BRG-research/compas_tf/data/FloorColumnConnection/4x/Artboard 1@4x.png

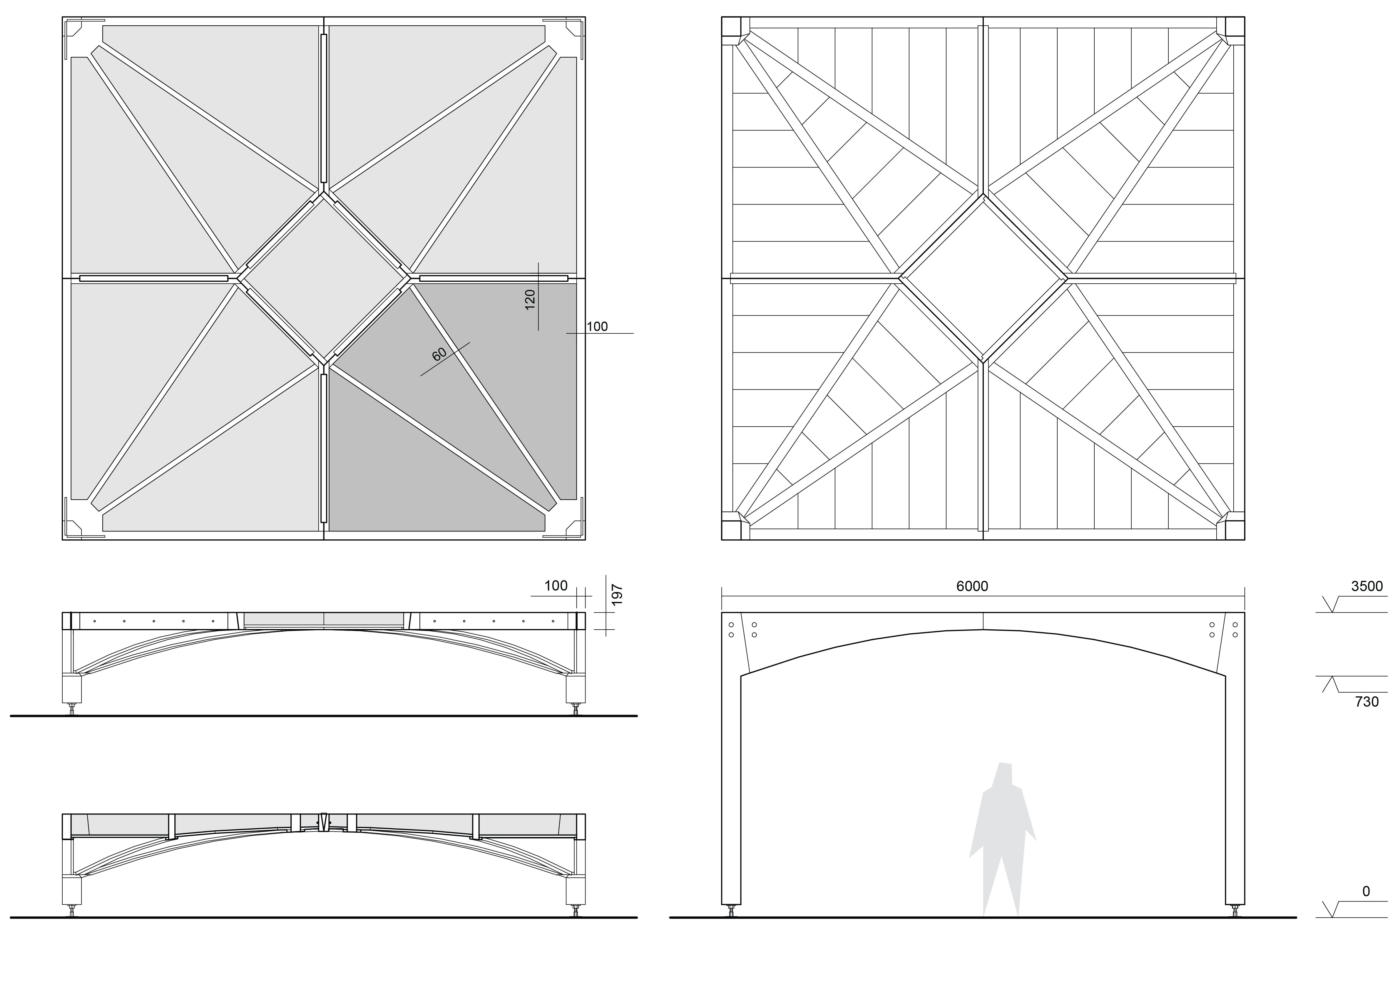
data/FloorColumnConnection/4x/Artboard 1@4x.png
