BRG-research/compas_tf/data/FloorColumnConnection/drawings.png

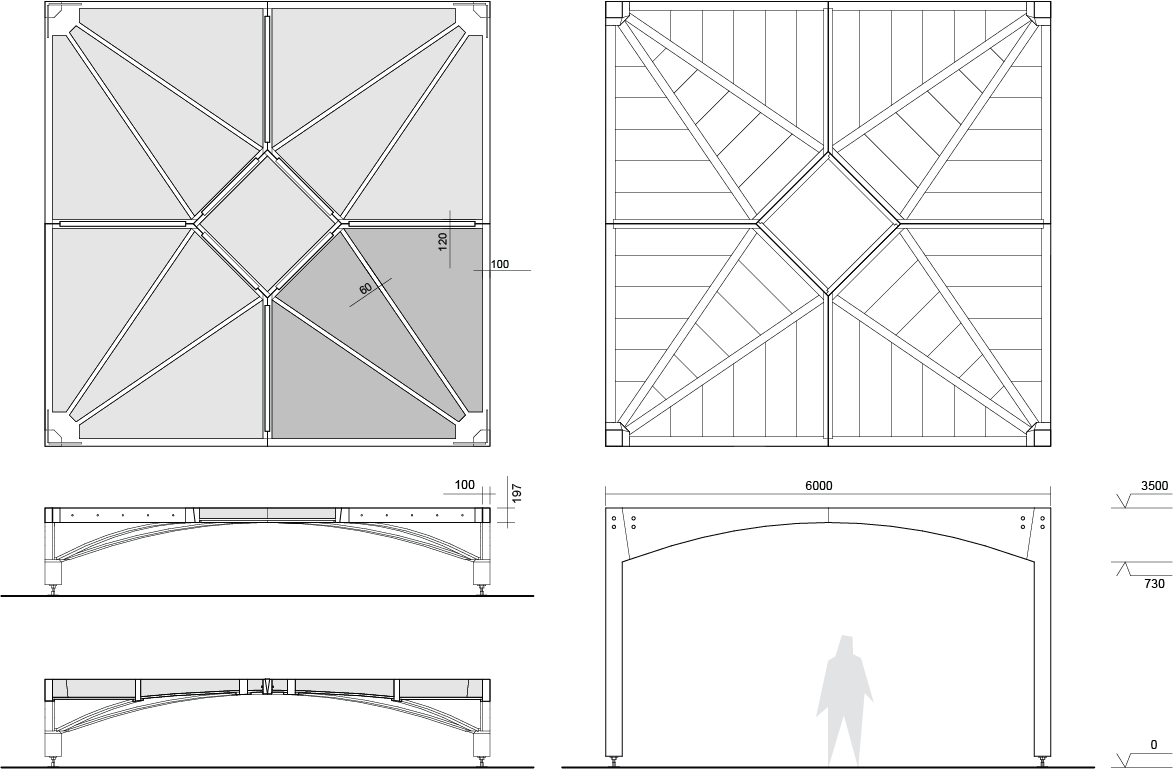
data/FloorColumnConnection/drawings.png
