BRG-research/compas_tf/data/total_station/total_station_es105_preview.jpg

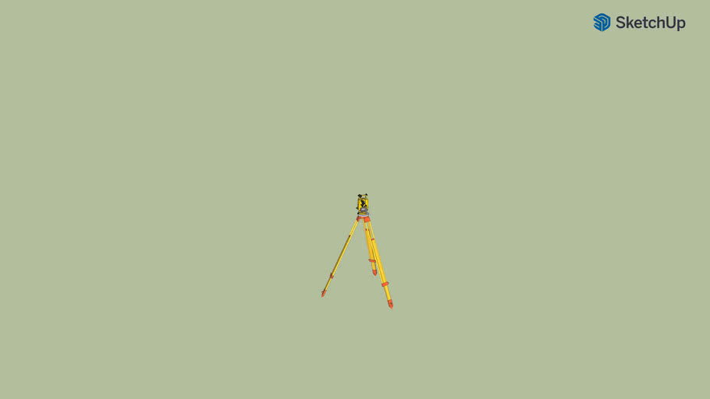
data/total_station/total_station_es105_preview.jpg
