BRG-research/compas_tf/docs/_images/1767874582386.jpg

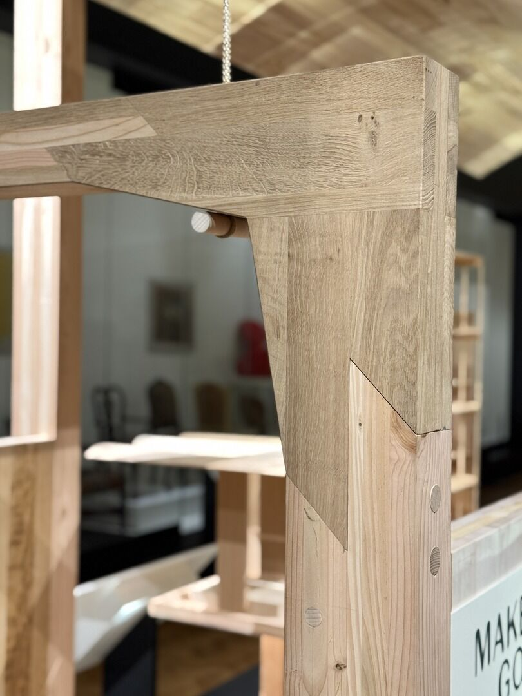
docs/_images/1767874582386.jpg
