BRG-research/compas_tf/docs/_images/column_head_connection3.png

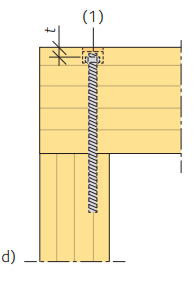
docs/_images/column_head_connection3.png
