BRG-research/compas_tf/docs/_images/column_head_connection.png

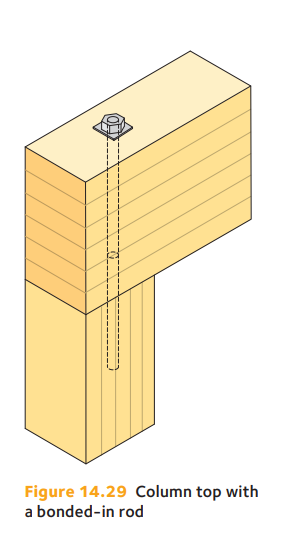
docs/_images/column_head_connection.png
