BRG-research/compas_tf/docs/_images/compresseion_perpendicular_to_grain.jpg

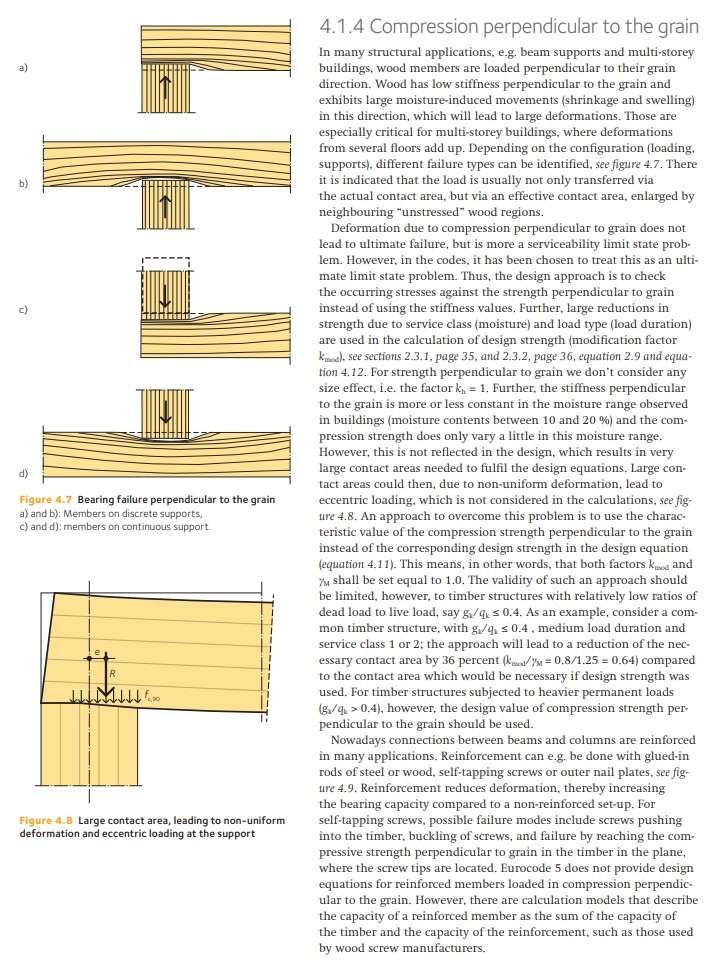
docs/_images/compresseion_perpendicular_to_grain.jpg
