BRG-research/compas_tf/docs/_images/compresseion_perpendicular_to_grain_2.jpg

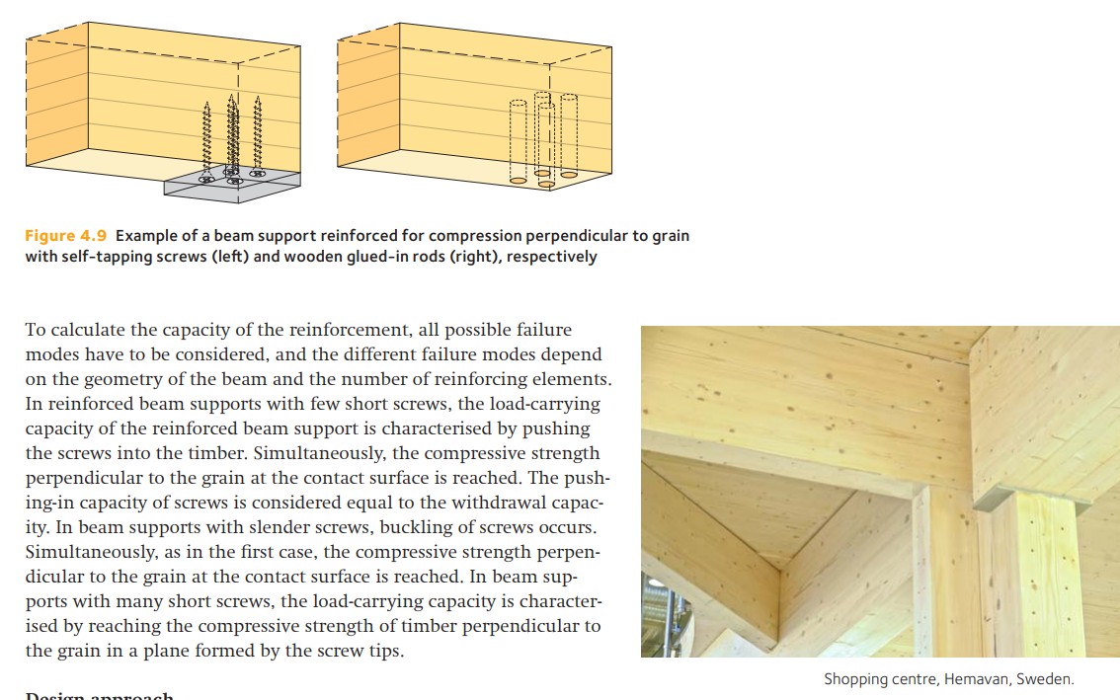
docs/_images/compresseion_perpendicular_to_grain_2.jpg
