BRG-research/compas_tf/docs/_images/icd_column_head_clt_fiber.png

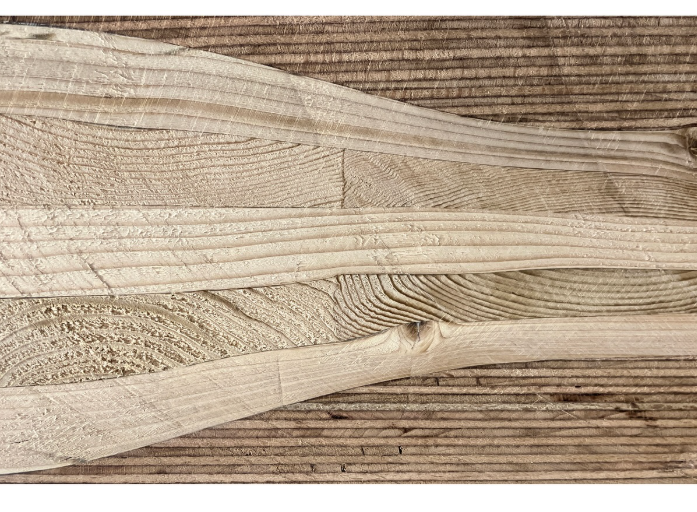
docs/_images/icd_column_head_clt_fiber.png
