BRG-research/compas_tf/docs/_images/model1.png

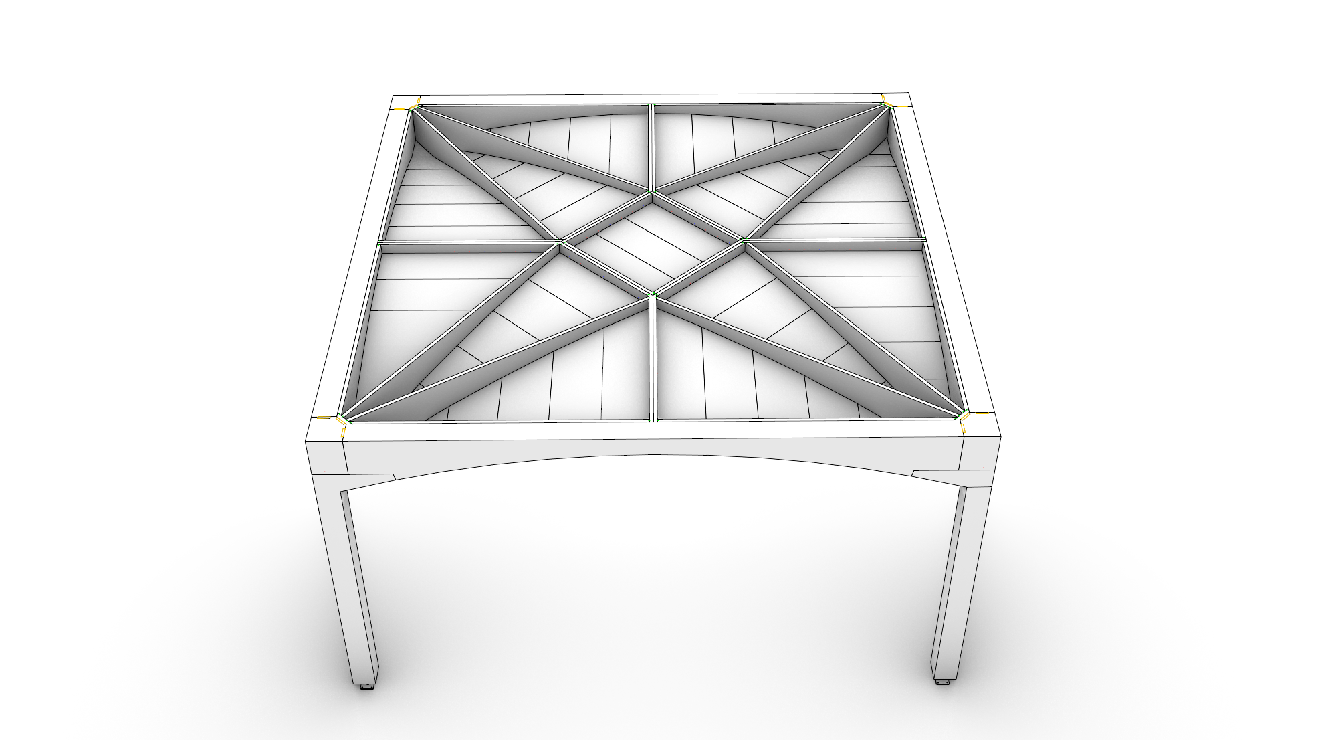
docs/_images/model1.png
