BRG-research/compas_tf/docs/_images/quarter1.png

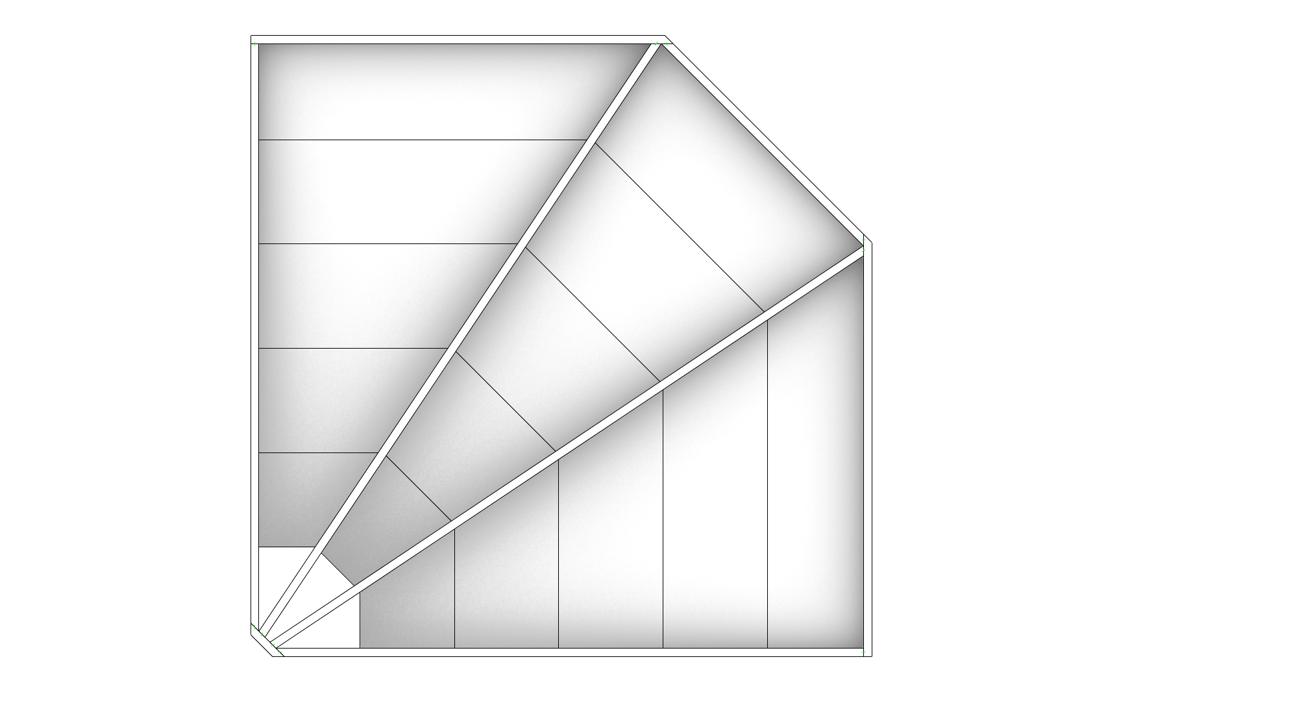
docs/_images/quarter1.png
