BRG-research/compas_tf/docs/_images/quarter2.png

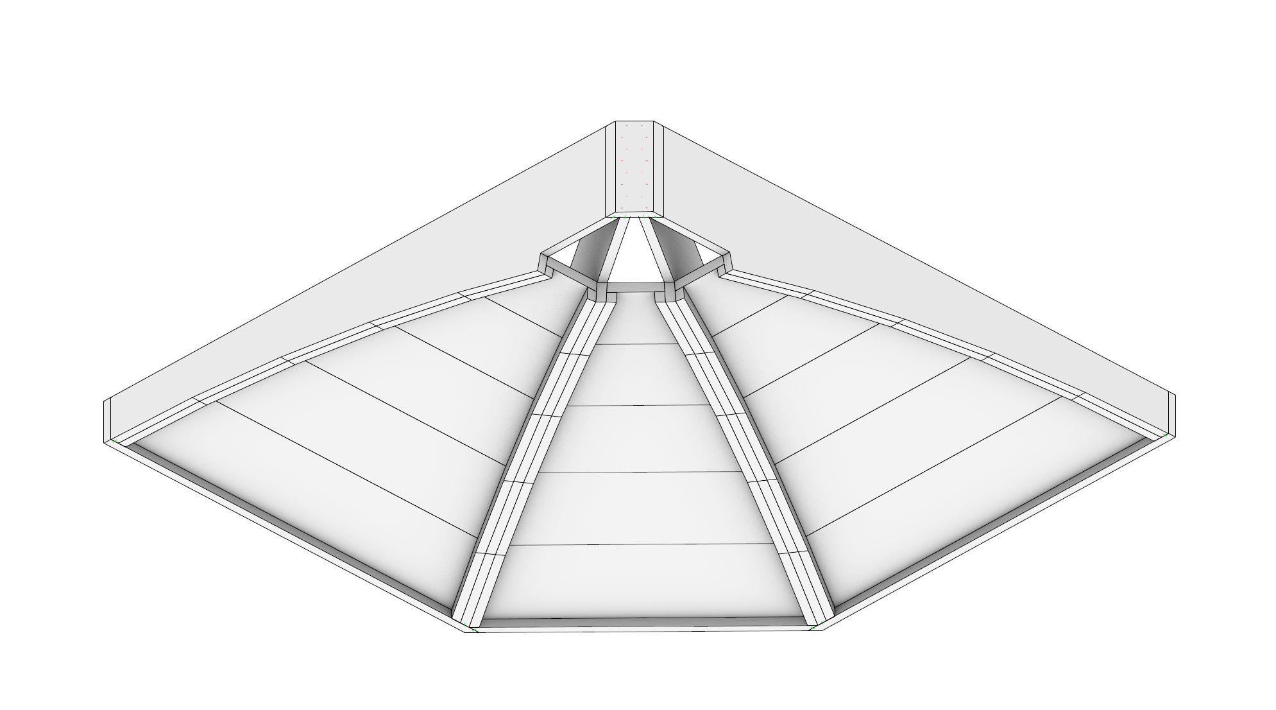
docs/_images/quarter2.png
