BRG-research/compas_tf/docs/_images/quarter3.png

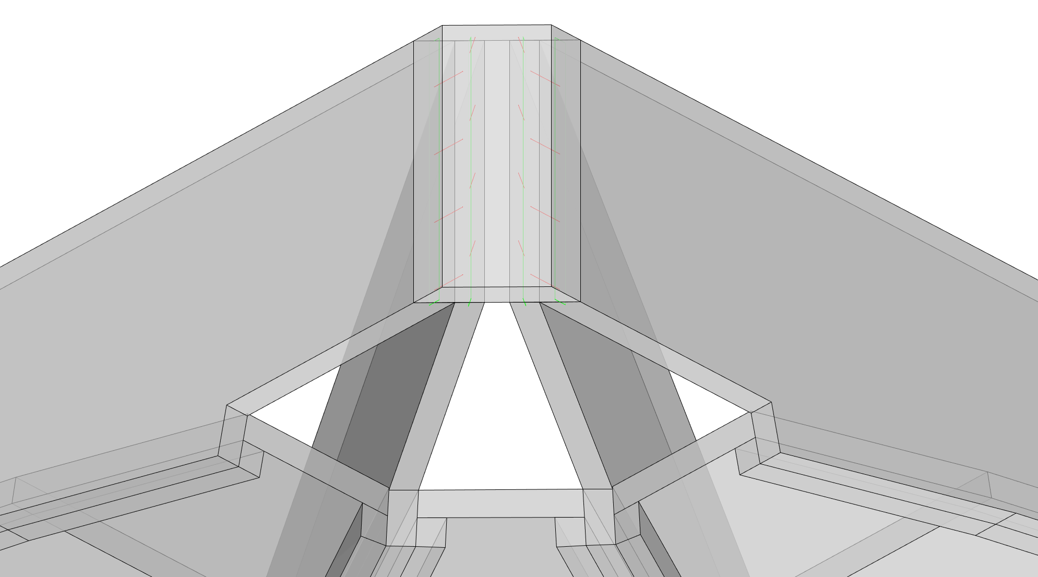
docs/_images/quarter3.png
