BRG-research/compas_tf/docs/_images/quarter4.png

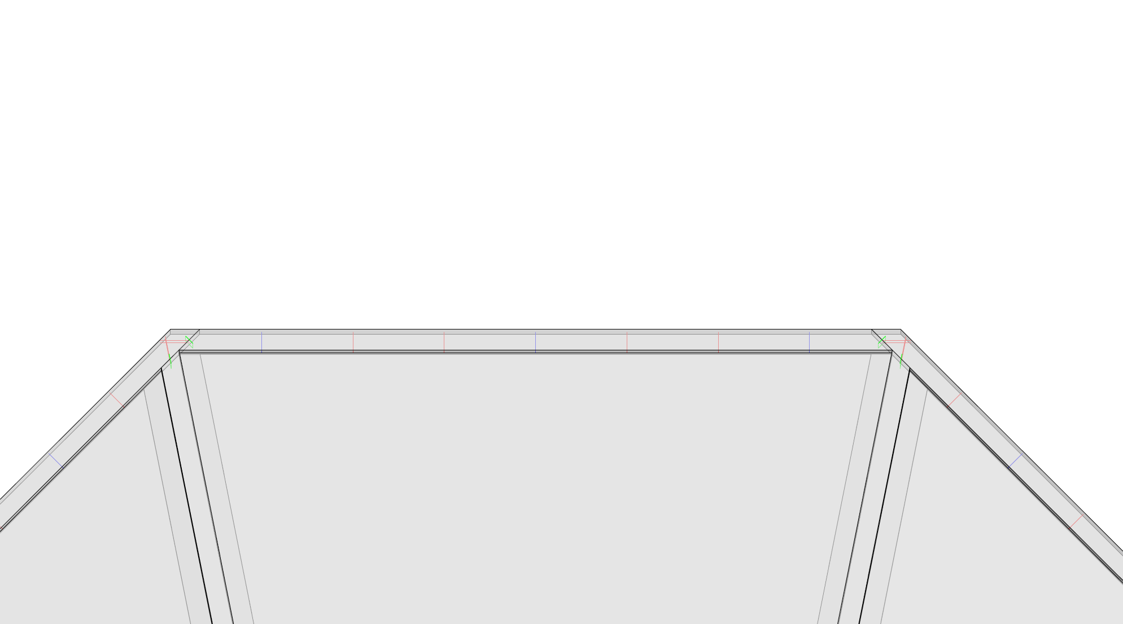
docs/_images/quarter4.png
