BRG-research/compas_tf/docs/_images/robeller_reciprocal.jpg

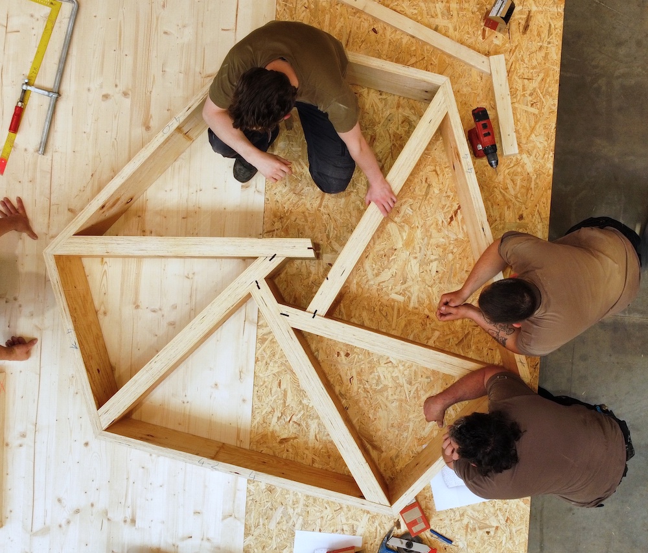
docs/_images/robeller_reciprocal.jpg
