BRG-research/compas_tf/docs/_images/screenshot_0.png

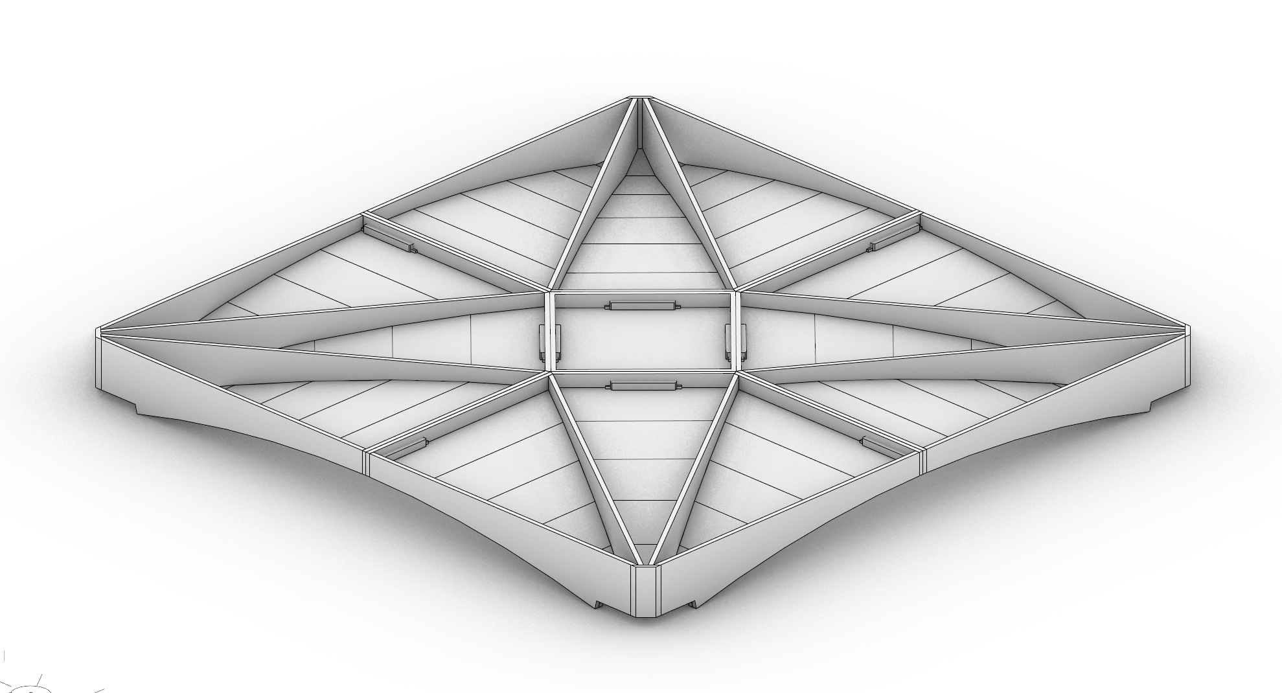
docs/_images/screenshot_0.png
