BRG-research/compas_tf/docs/_images/screenshot_1.png

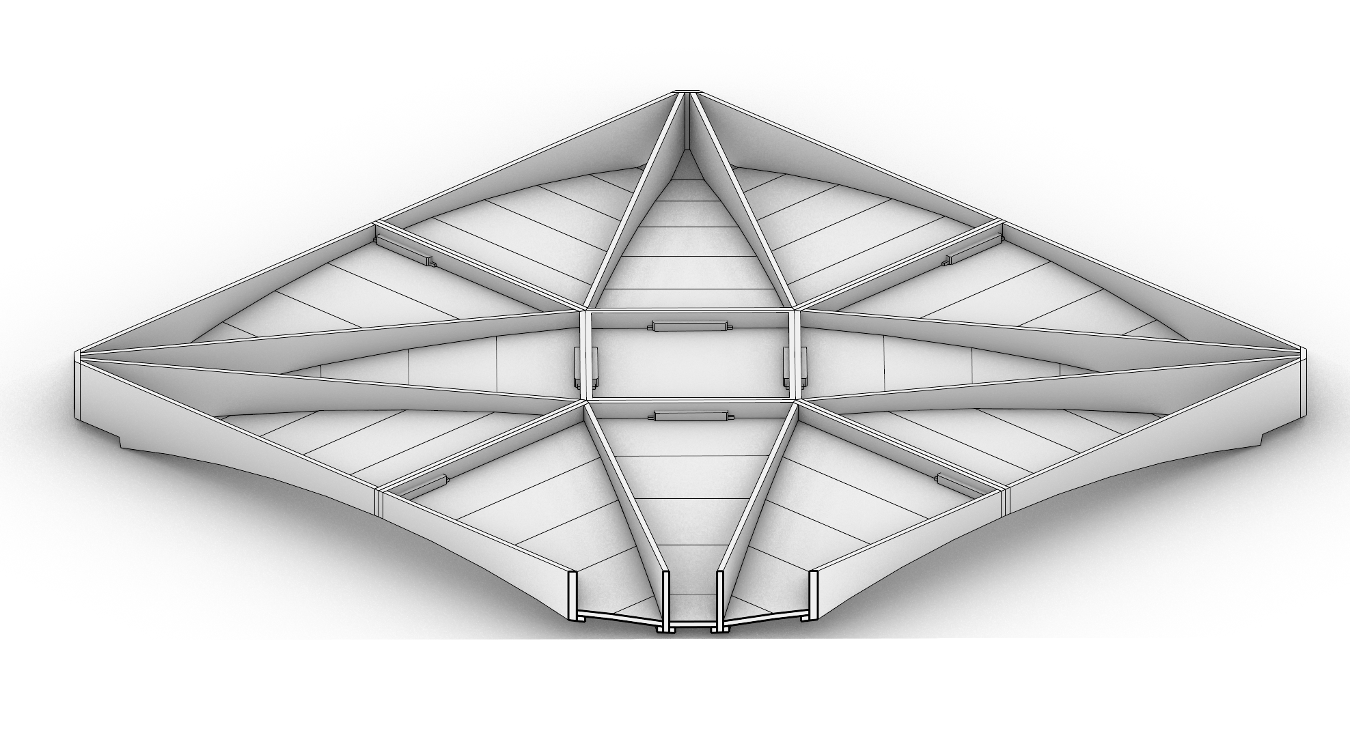
docs/_images/screenshot_1.png
