BRG-research/compas_tf/docs/_images/screenshot_2.png

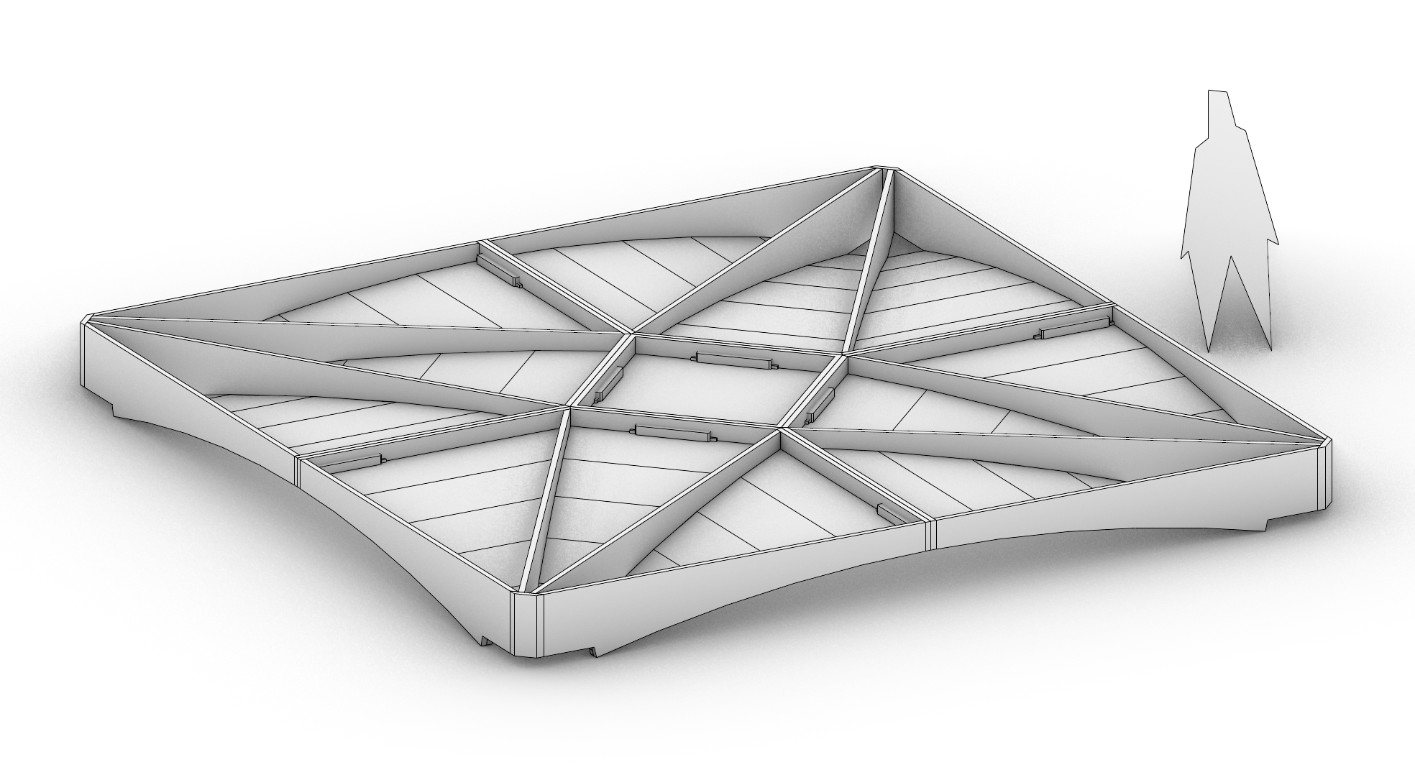
docs/_images/screenshot_2.png
