BRG-research/compas_tf/docs/_images/screenshot_3.png

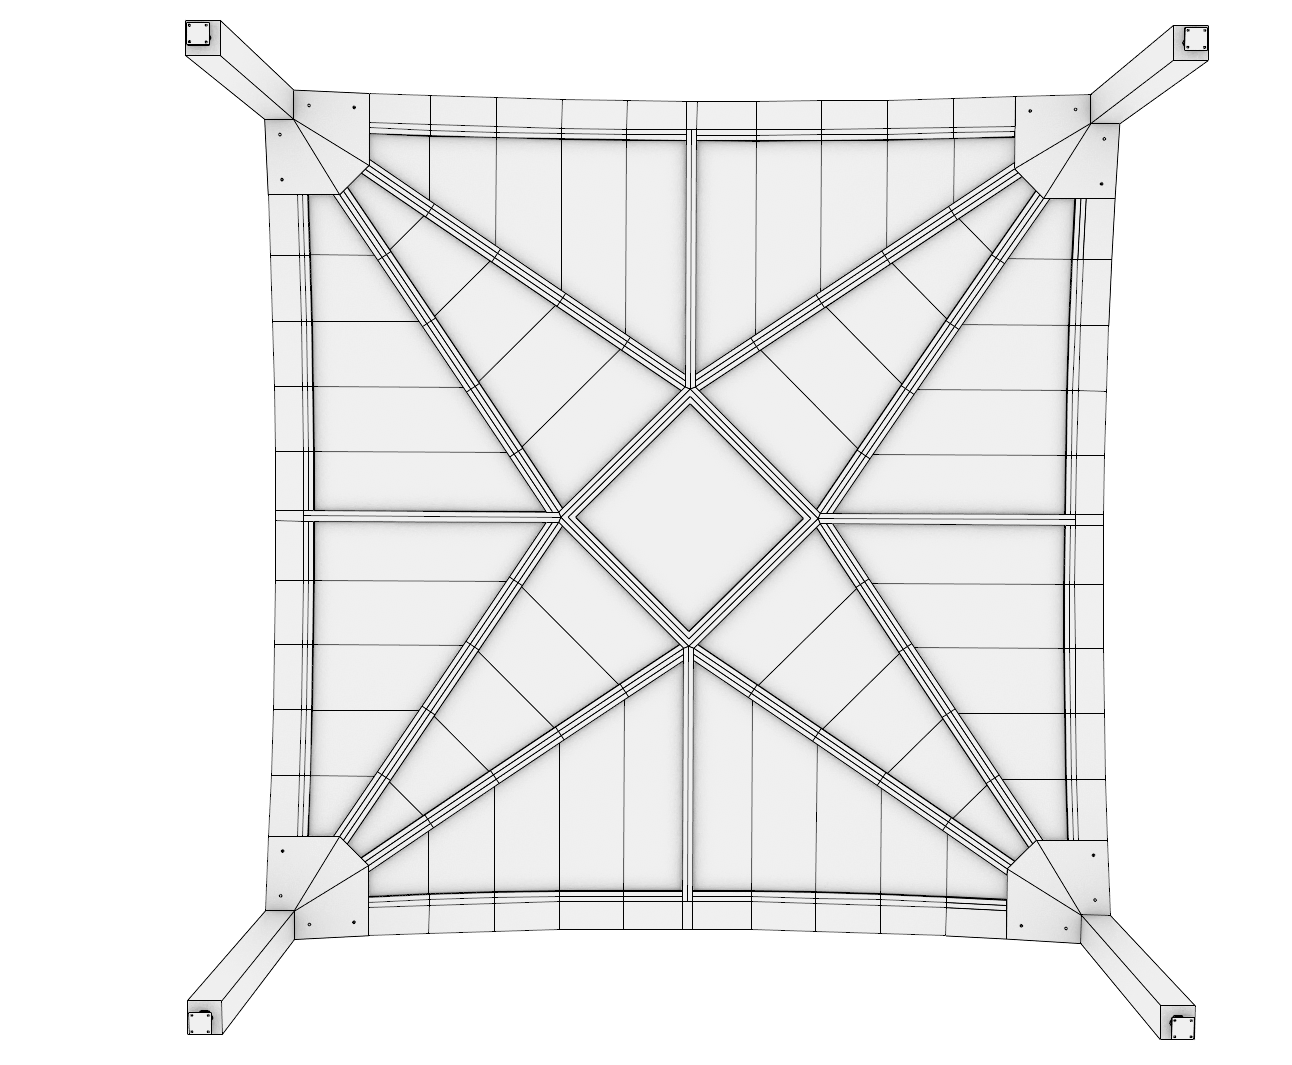
docs/_images/screenshot_3.png
