BRG-research/compas_tf/docs/_images/screenshot_5.png

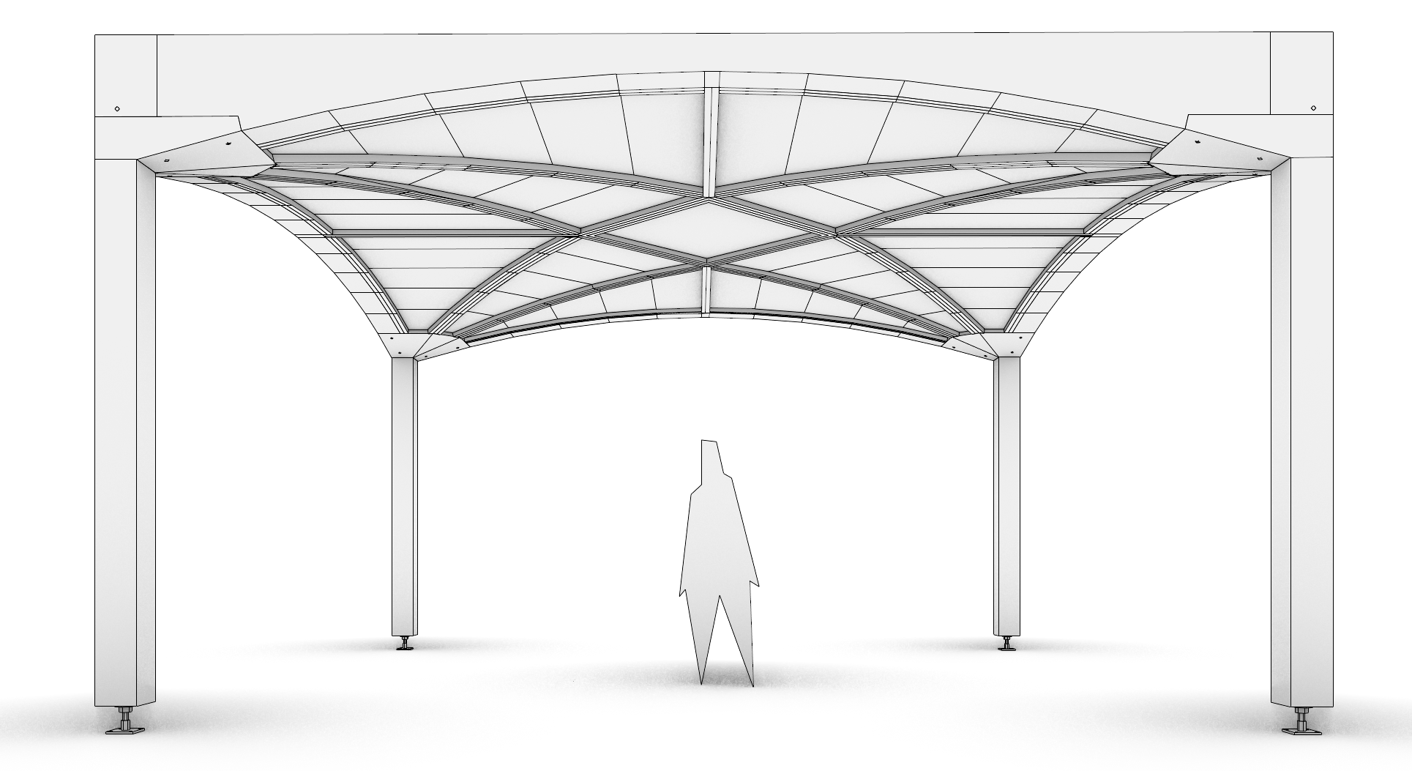
docs/_images/screenshot_5.png
