BRG-research/compas_tf/docs/references/autobahn_a1_pirmin_jung.png

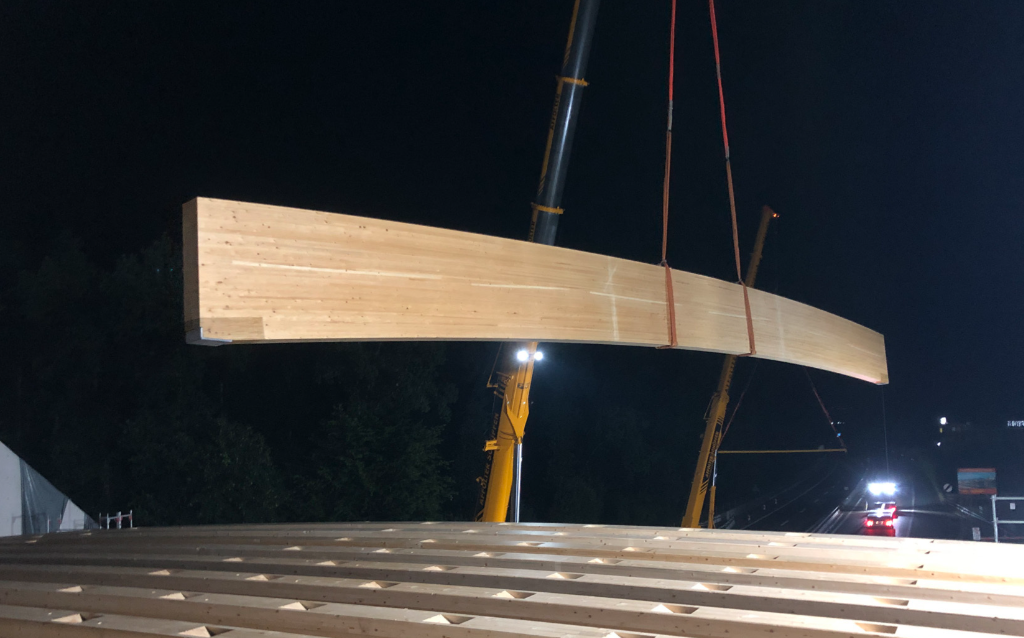
docs/references/autobahn_a1_pirmin_jung.png
