BRG-research/compas_tf/src/compas_tf/data/column_base_power_base_sherpa_150402_PB_L-140-C.obj

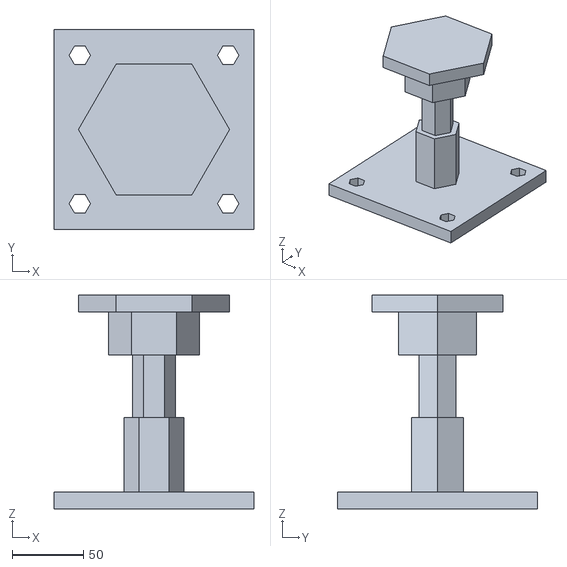
[picture p47: CAD file, 2026-01-28]
src/compas_tf/data/column_base_power_base_sherpa_150402_PB_L-140-C.obj
140.0 x 140.0 x 150.0
