BRG-research/compas_tf/src/compas_tf/data/OuterRibConnector/OuterRibConnector_Result.obj

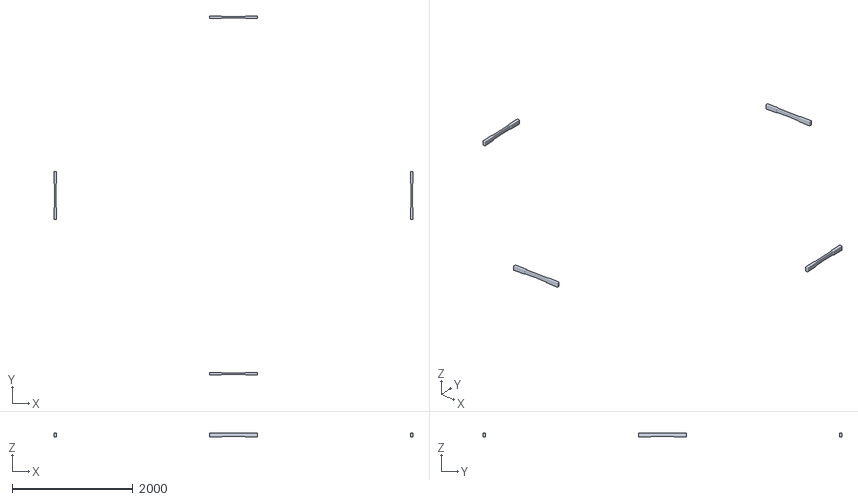
[picture p48: CAD file, 2026-08-09]
src/compas_tf/data/OuterRibConnector/OuterRibConnector_Result.obj
5940.0 x 5940.0 x 70.4
