BRG-research/compas_tf/data/column_base_power_base_sherpa_150402_PB_L-140-C.ply

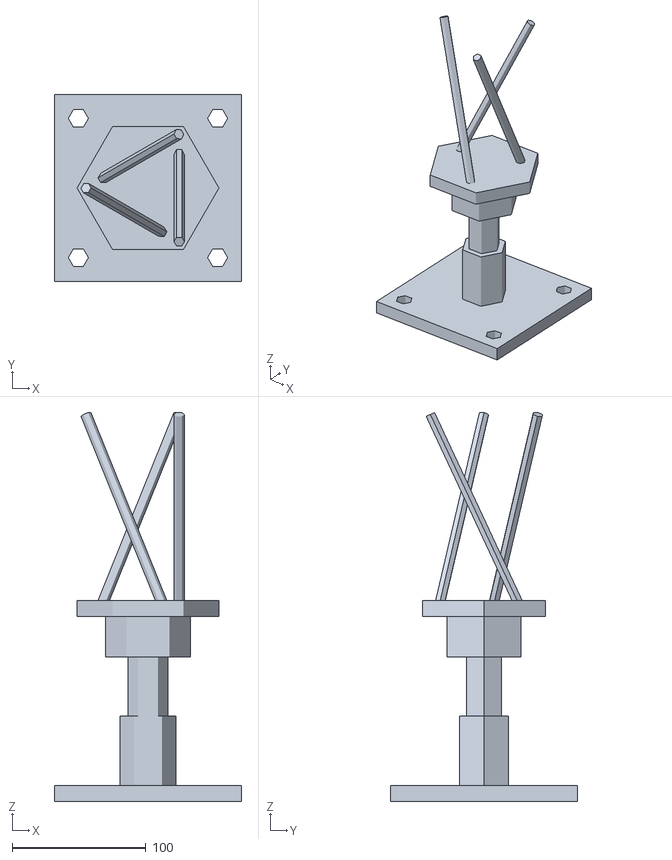
[picture p49: CAD file, 2026-01-28]
data/column_base_power_base_sherpa_150402_PB_L-140-C.ply
140.0 x 140.0 x 290.6
