BRG-research/compas_tf/data/fabrication/wedges_inner_beams_0_fab.stp

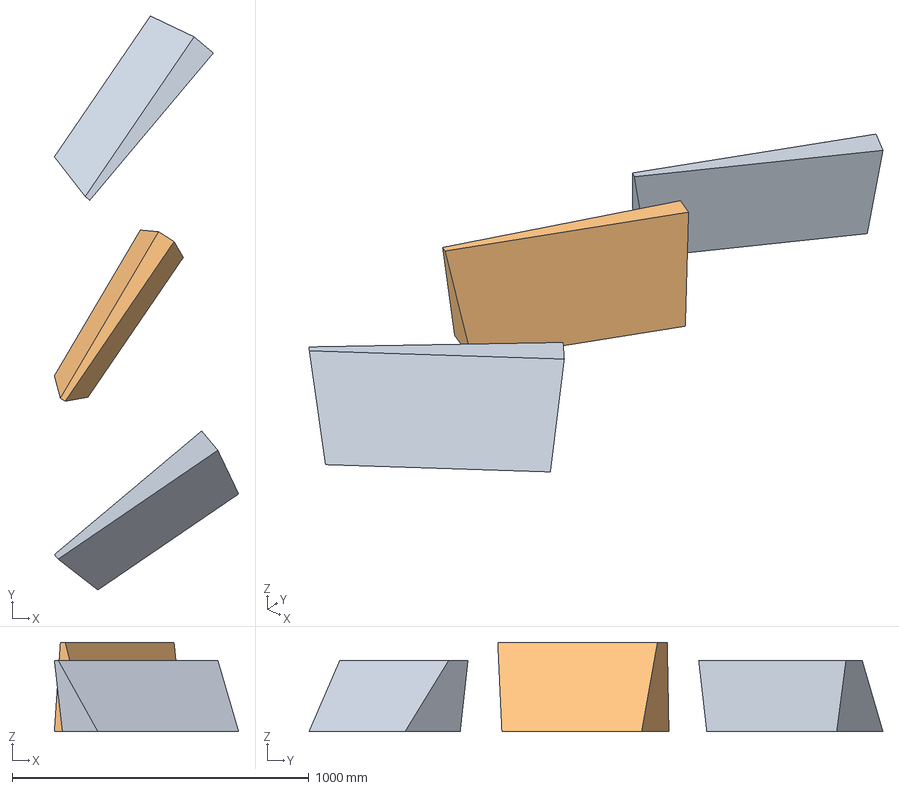
[picture p50: CAD file, 2026-08-25]
data/fabrication/wedges_inner_beams_0_fab.stp
620.7 x 1932.8 x 300.0 mm
wedges_inner_beams_0_fab 1.1
wedges_inner_beams_0_fab 1.2
wedges_inner_beams_0_fab 1.3
wedges_inner_beams_0_fab 1.4
wedges_inner_beams_0_fab 1.5
wedges_inner_beams_0_fab 1.6
