BRG-research/compas_tf/data/SchoringElement/schoring_vertical_body_start_0.obj

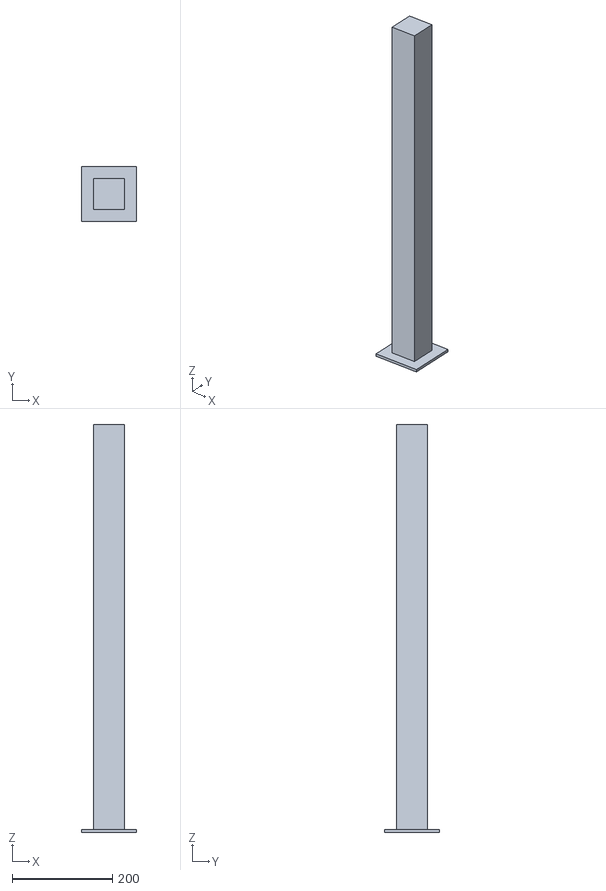
[picture p51: CAD file, 2026-04-22]
data/SchoringElement/schoring_vertical_body_start_0.obj
110.0 x 110.0 x 814.0
