BRG-research/compas_tf/src/compas_tf/data/OuterRibConnector/OuterRibConnector.obj

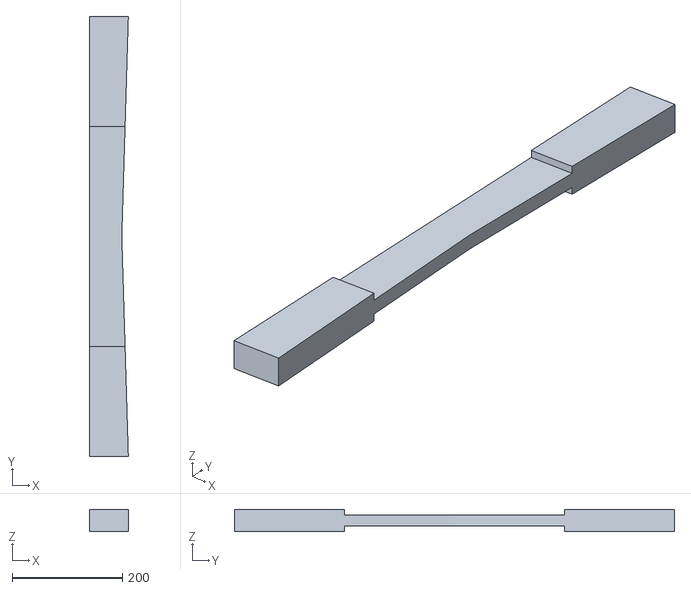
[picture p52: CAD file, 2026-08-09]
src/compas_tf/data/OuterRibConnector/OuterRibConnector.obj
70.4 x 800.0 x 40.0
