BRG-research/compas_tf/data/fabrication/column_0_preview.obj

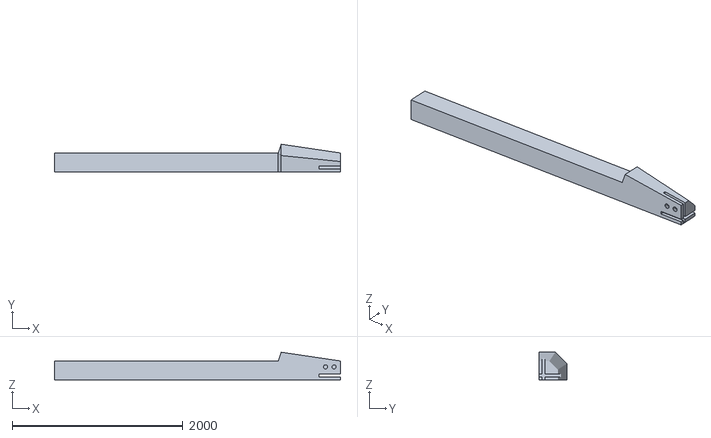
[picture p54: CAD file, 2026-08-25]
data/fabrication/column_0_preview.obj
3350.0 x 323.0 x 323.0
