BRG-research/compas_tf/src/compas_tf/data/OuterRibConnector/OuterRibConnector_cut0.obj

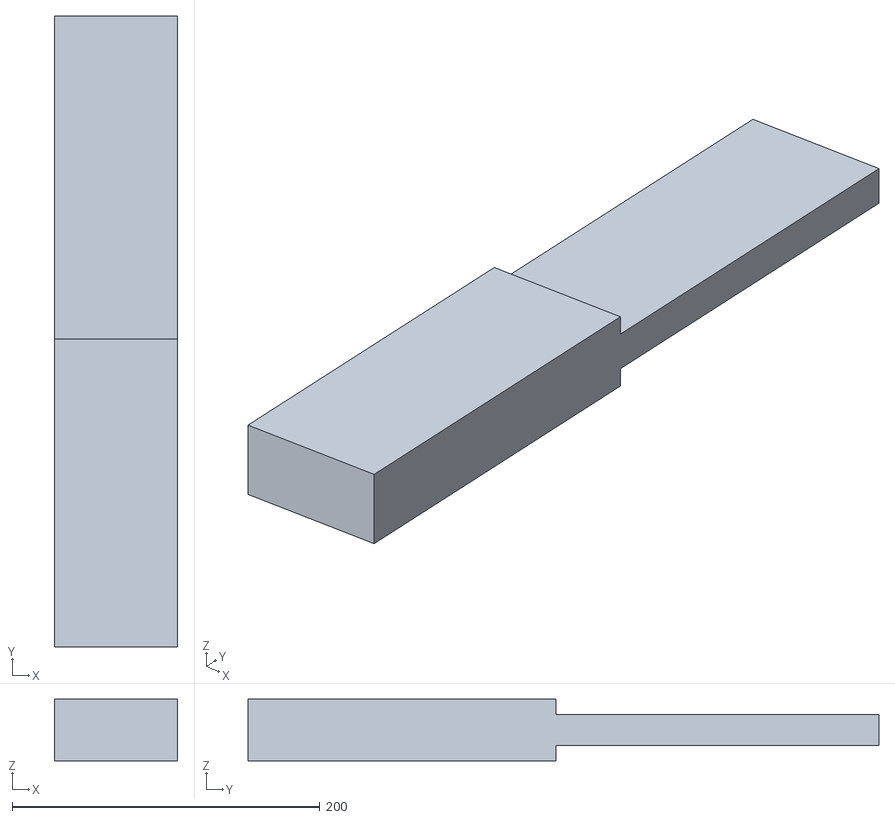
[picture p56: CAD file, 2026-08-09]
src/compas_tf/data/OuterRibConnector/OuterRibConnector_cut0.obj
80.0 x 410.0 x 40.0
