BRG-research/compas_tf/data/beam_column_head_connection_180413_Sherpa_XL120_8x160_3D_detailed.obj

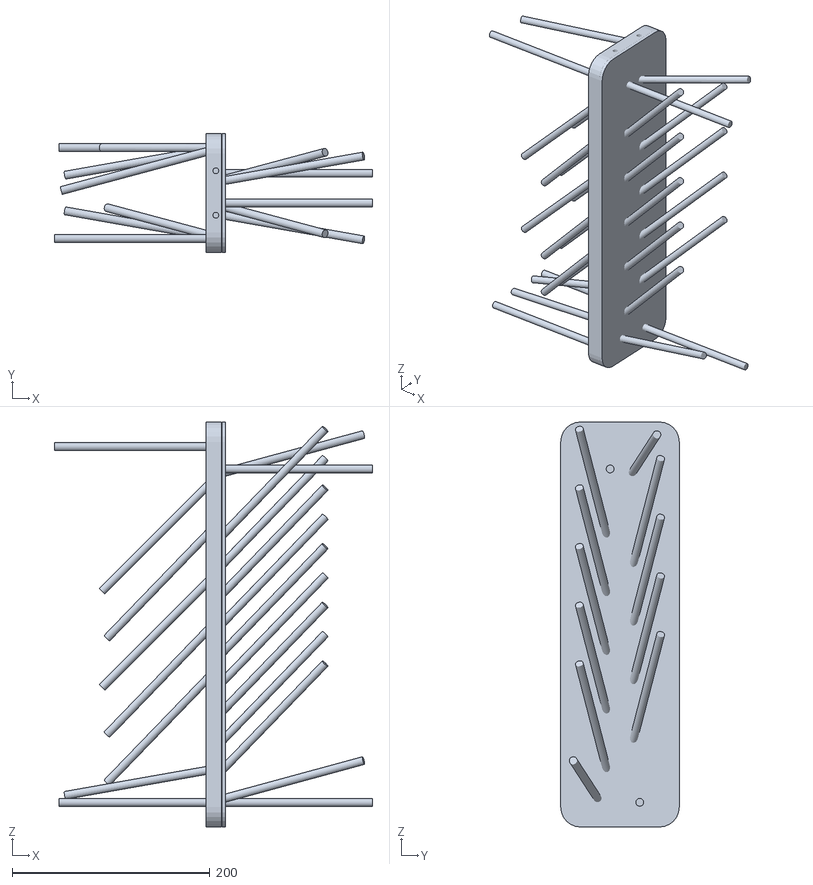
[picture p57: CAD file, 2026-01-28]
data/beam_column_head_connection_180413_Sherpa_XL120_8x160_3D_detailed.obj
322.2 x 120.0 x 410.0
