BRG-research/compas_tf/data/fabrication/connector_0_fab.stp

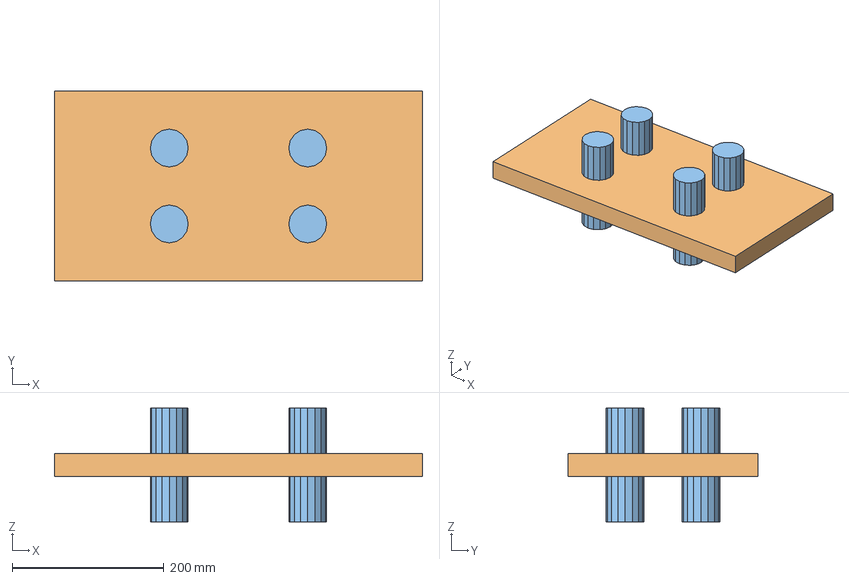
[picture p58: CAD file, 2026-08-25]
data/fabrication/connector_0_fab.stp
485.0 x 250.0 x 150.0 mm
connector_0_fab 1.1
connector_0_fab 1.2
connector_0_fab 1.3
connector_0_fab 1.4
connector_0_fab 1.5
connector_0_fab 1.6
