BRG-research/compas_tf/data/SchoringElement/schoring_vertical_body_end_5.obj

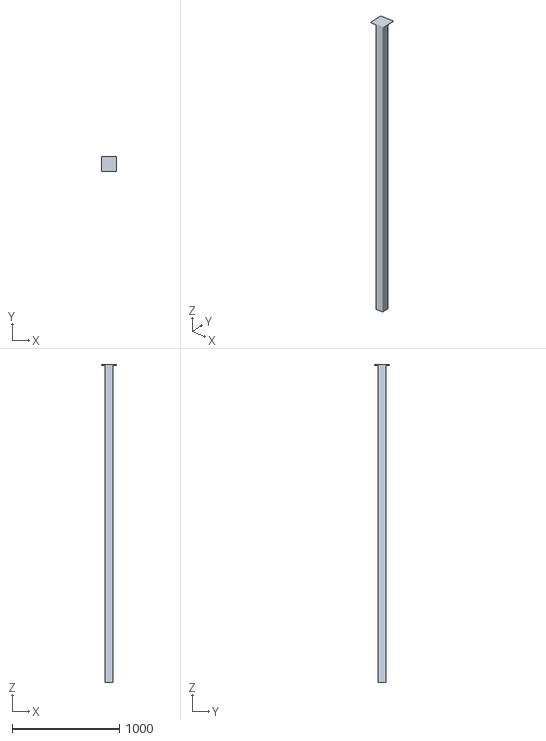
[picture p59: CAD file, 2026-04-22]
data/SchoringElement/schoring_vertical_body_end_5.obj
140.0 x 140.0 x 2965.0
