BRG-research/compas_tf/data/fabrication/connector_0_preview.obj

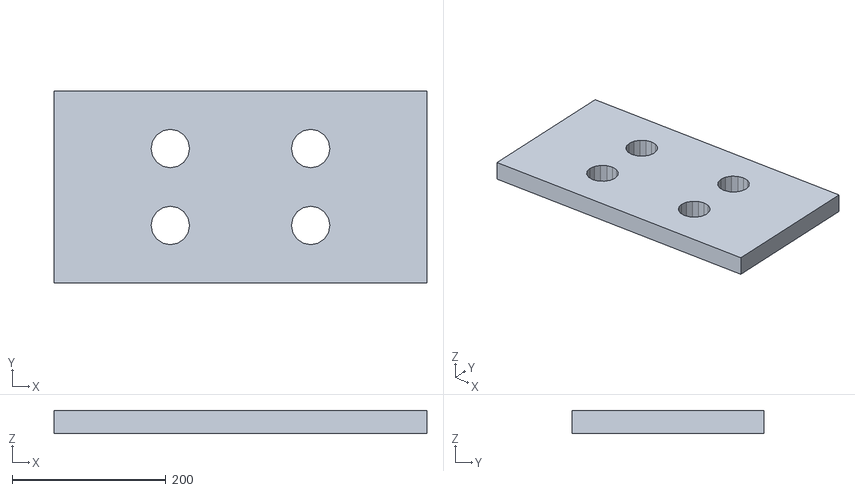
[picture p60: CAD file, 2026-08-25]
data/fabrication/connector_0_preview.obj
485.0 x 250.0 x 30.0
