BRG-research/compas_tf/data/fabrication/inner_beams_2_0_preview.obj

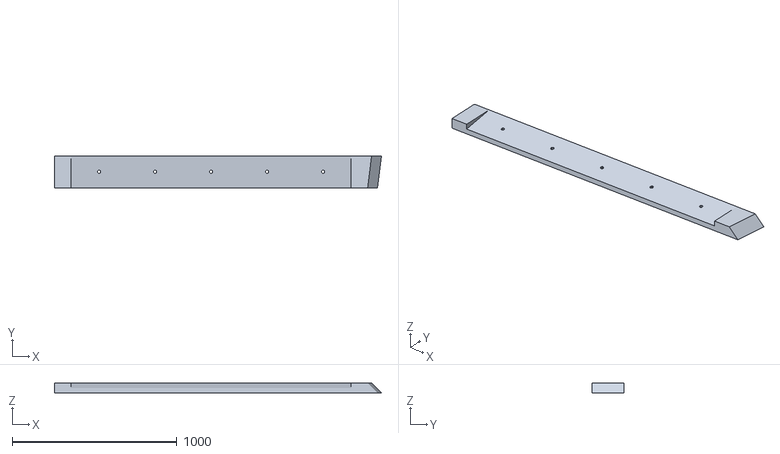
[picture p62: CAD file, 2026-08-25]
data/fabrication/inner_beams_2_0_preview.obj
1984.4 x 197.0 x 60.0
