BRG-research/compas_tf/data/SchoringElement/custom_head0.obj

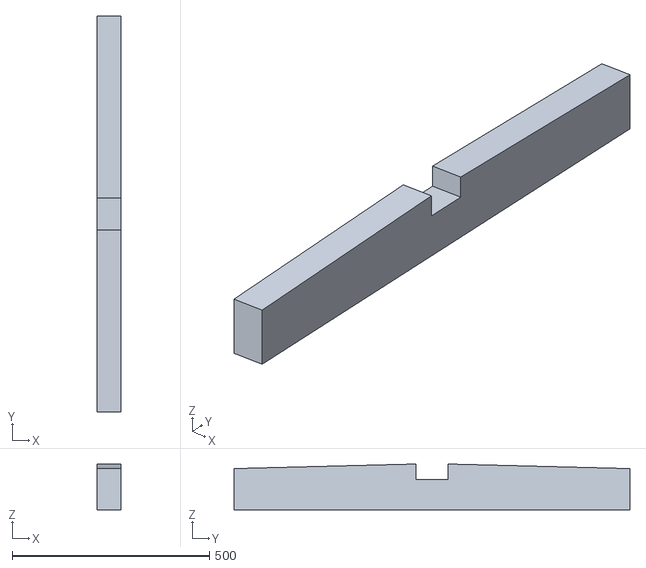
[picture p63: CAD file, 2026-04-22]
data/SchoringElement/custom_head0.obj
60.0 x 1004.0 x 116.6
