BRG-research/compas_tf/data/fabrication/tsections_0_fab.stp

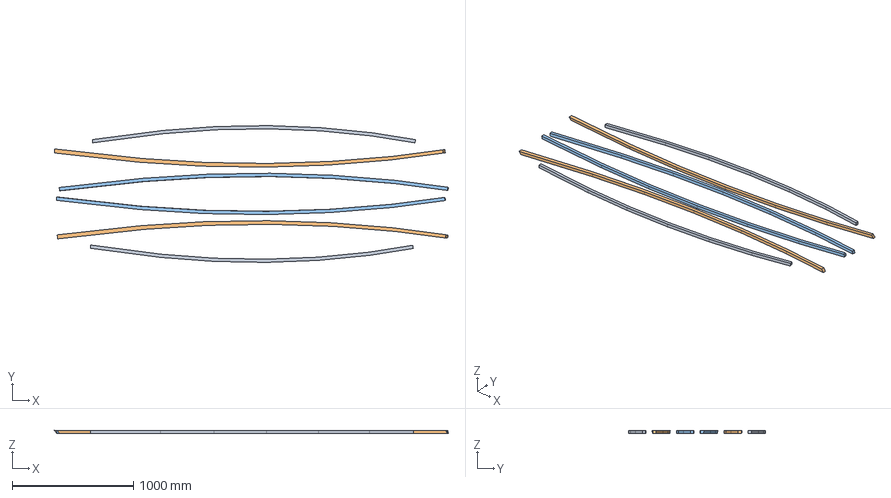
[picture p64: CAD file, 2026-08-25]
data/fabrication/tsections_0_fab.stp
3255.2 x 1130.6 x 27.0 mm
tsections_0_fab 1.1
tsections_0_fab 1.2
tsections_0_fab 1.3
tsections_0_fab 1.4
tsections_0_fab 1.5
tsections_0_fab 1.6
tsections_0_fab 1.7
tsections_0_fab 1.8
tsections_0_fab 1.9
tsections_0_fab 1.10
tsections_0_fab 1.11
tsections_0_fab 1.12
