BRG-research/compas_tf/data/SchoringElement/schoring_vertical_body_end_2.obj

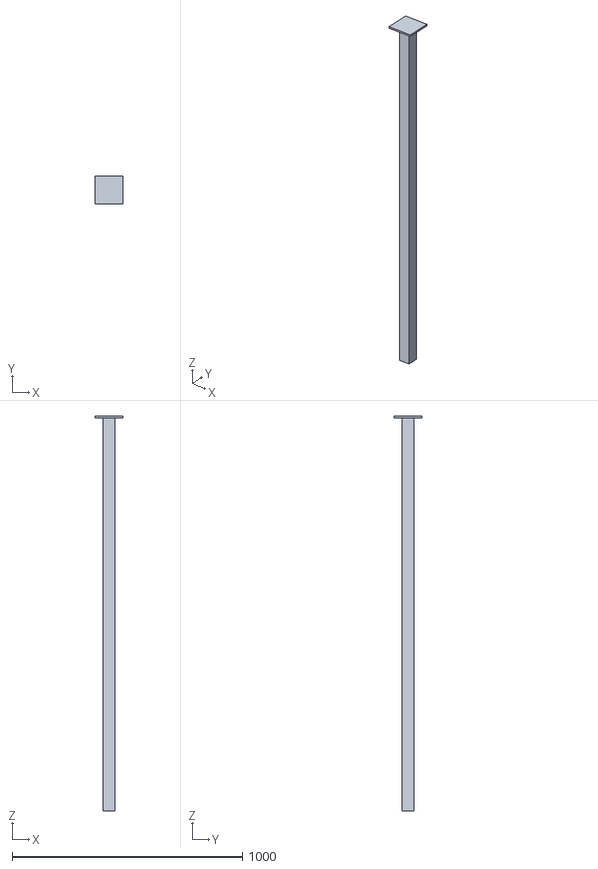
[picture p65: CAD file, 2026-04-22]
data/SchoringElement/schoring_vertical_body_end_2.obj
120.0 x 120.0 x 1715.0
