BRG-research/compas_tf/data/fabrication/inner_beams_0_0_fab.stp

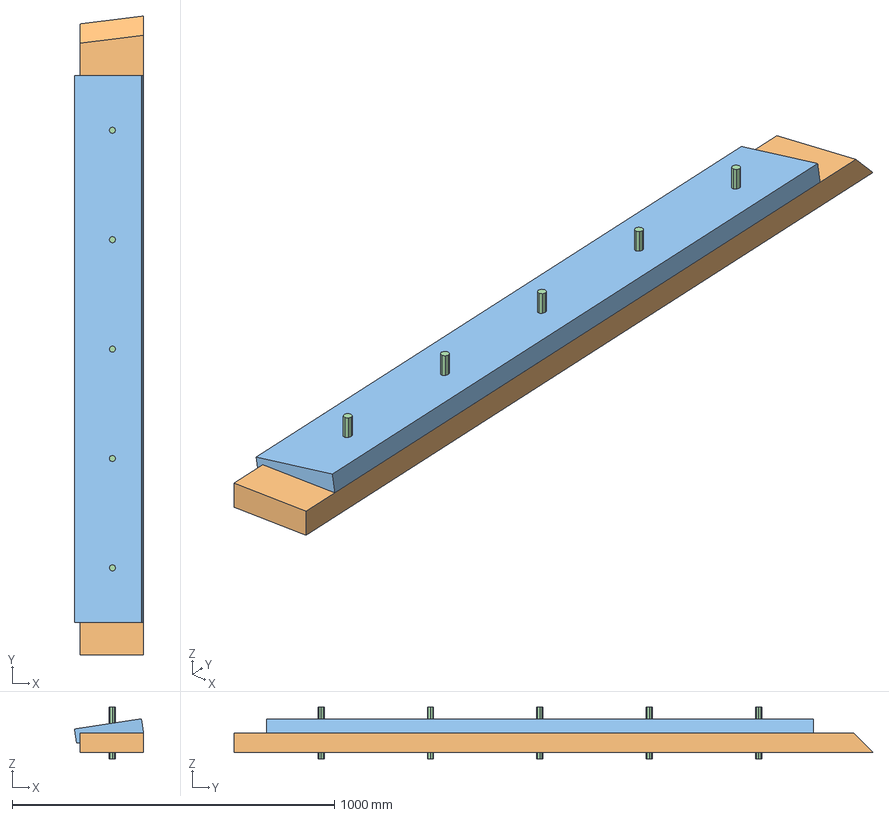
[picture p66: CAD file, 2026-08-25]
data/fabrication/inner_beams_0_0_fab.stp
215.3 x 1984.4 x 160.0 mm
inner_beams_0_0_fab 1.1
inner_beams_0_0_fab 1.2
inner_beams_0_0_fab 1.3
inner_beams_0_0_fab 1.4
inner_beams_0_0_fab 1.5
inner_beams_0_0_fab 1.6
inner_beams_0_0_fab 1.7
inner_beams_0_0_fab 1.8
