BRG-research/compas_tf/data/SchoringElement/schoring_vertical_body_end_0.obj

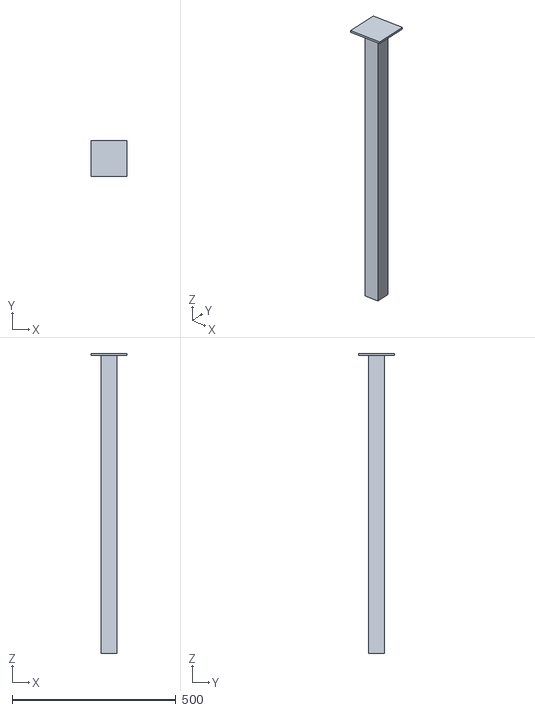
[picture p67: CAD file, 2026-04-22]
data/SchoringElement/schoring_vertical_body_end_0.obj
110.0 x 110.0 x 915.0
