BRG-research/compas_tf/data/fabrication/outer_ribs_0_0_fab.stp

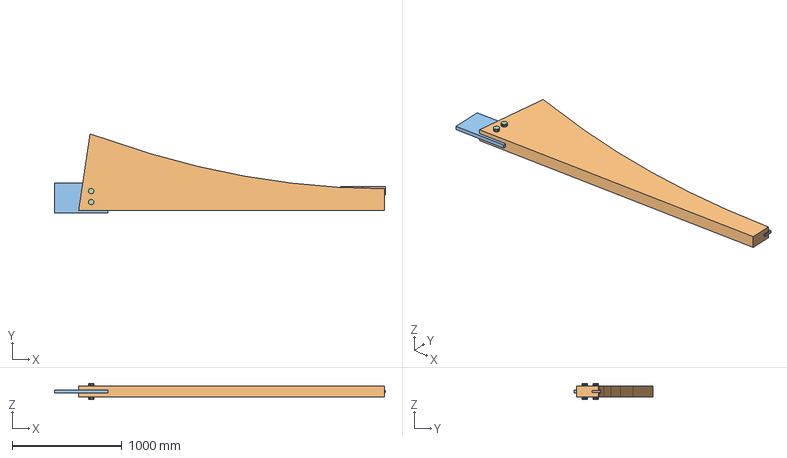
[picture p68: CAD file, 2026-08-25]
data/fabrication/outer_ribs_0_0_fab.stp
3010.0 x 719.8 x 150.0 mm
outer_ribs_0_0_fab 1.1
outer_ribs_0_0_fab 1.2
outer_ribs_0_0_fab 1.3
outer_ribs_0_0_fab 1.4
outer_ribs_0_0_fab 1.5
outer_ribs_0_0_fab 1.6
