BRG-research/compas_tf/data/fabrication/beds_0_fab.stp

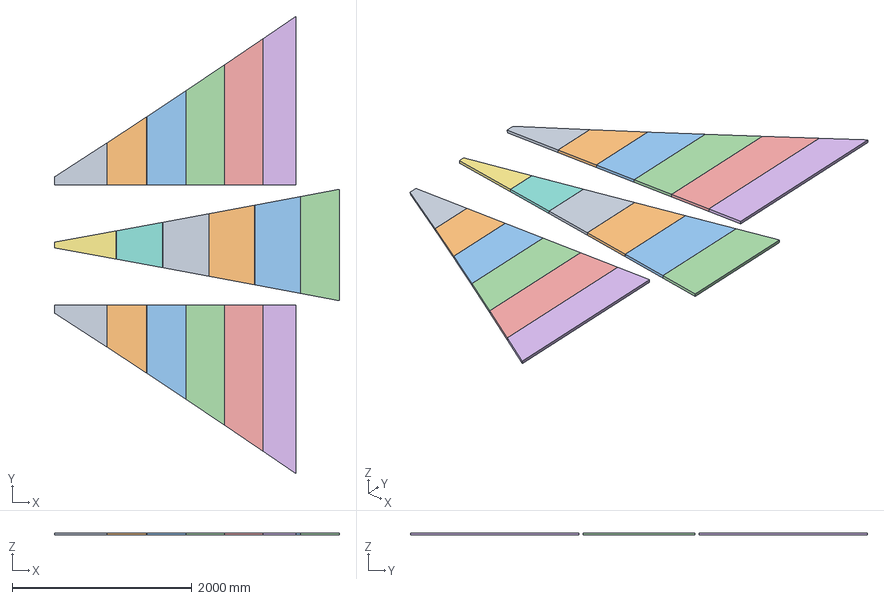
[picture p70: CAD file, 2026-08-25]
data/fabrication/beds_0_fab.stp
3175.0 x 5092.7 x 27.5 mm
beds_0_fab 1.1
beds_0_fab 1.2
beds_0_fab 1.3
beds_0_fab 1.4
beds_0_fab 1.5
beds_0_fab 1.6
beds_0_fab 1.7
beds_0_fab 1.8
beds_0_fab 1.9
beds_0_fab 1.10
beds_0_fab 1.11
beds_0_fab 1.12
beds_0_fab 1.13
beds_0_fab 1.14
beds_0_fab 1.15
beds_0_fab 1.16
beds_0_fab 1.17
beds_0_fab 1.18
beds_0_fab 1.19
beds_0_fab 1.20
beds_0_fab 1.21
beds_0_fab 1.22
beds_0_fab 1.23
beds_0_fab 1.24
beds_0_fab 1.25
beds_0_fab 1.26
beds_0_fab 1.27
beds_0_fab 1.28
beds_0_fab 1.29
beds_0_fab 1.30
beds_0_fab 1.31
beds_0_fab 1.32
beds_0_fab 1.33
beds_0_fab 1.34
beds_0_fab 1.35
beds_0_fab 1.36
