BRG-research/compas_tf/data/SchoringElement/schoring_vertical_body_start_4.obj

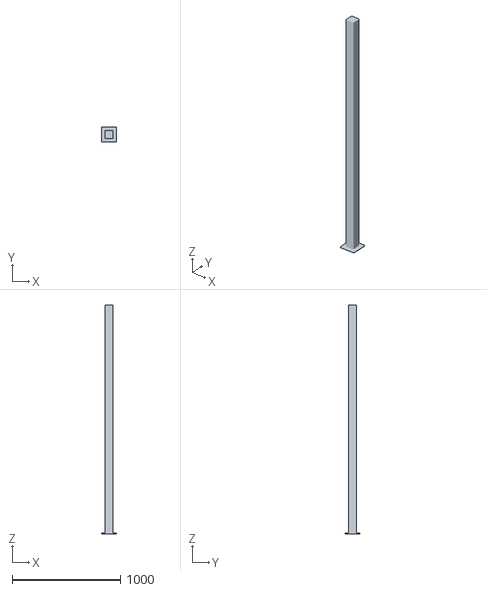
[picture p71: CAD file, 2026-04-22]
data/SchoringElement/schoring_vertical_body_start_4.obj
140.0 x 140.0 x 2114.0
