BRG-research/compas_tf/data/fabrication/connector_wedge_0_fab.stp

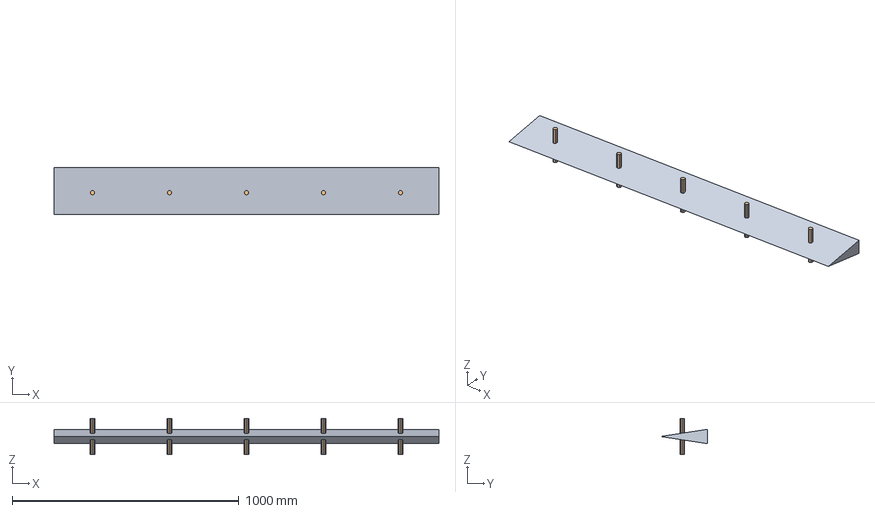
[picture p72: CAD file, 2026-08-25]
data/fabrication/connector_wedge_0_fab.stp
1698.8 x 208.5 x 160.0 mm
connector_wedge_0_fab 2.1
connector_wedge_0_fab 2.2
connector_wedge_0_fab 2.3
connector_wedge_0_fab 2.4
connector_wedge_0_fab 2.5
connector_wedge_0_fab 2.6
