BRG-research/compas_tf/data/SchoringElement/schoring_vertical_body_end_4.obj

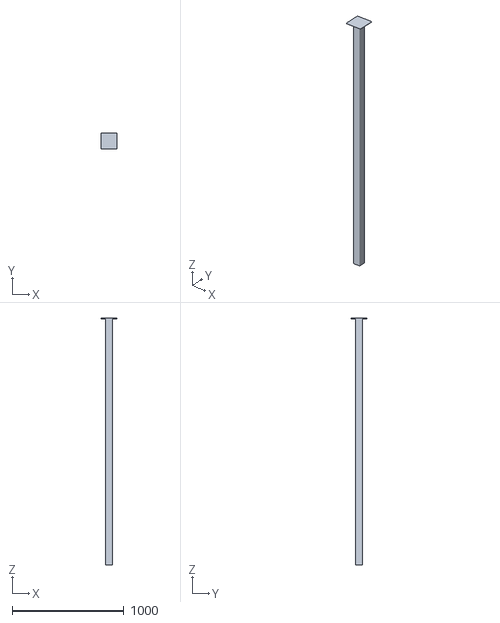
[picture p73: CAD file, 2026-04-22]
data/SchoringElement/schoring_vertical_body_end_4.obj
140.0 x 140.0 x 2215.0
