BRG-research/compas_tf/data/fabrication/dowel_0_fab.stp

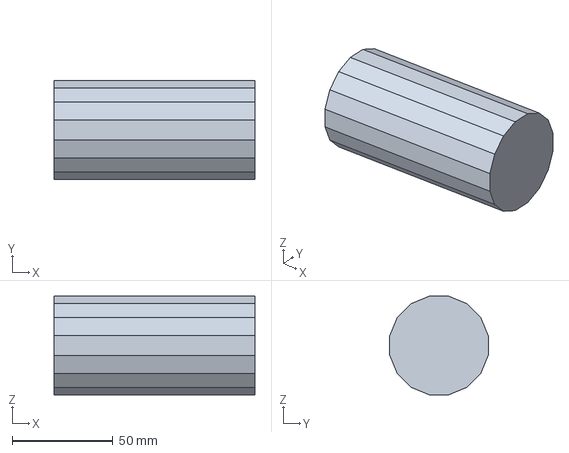
[picture p74: CAD file, 2026-08-25]
data/fabrication/dowel_0_fab.stp
100.0 x 49.0 x 49.0 mm
