BRG-research/compas_tf/data/fabrication/inner_ribs_0_0_fab.stp

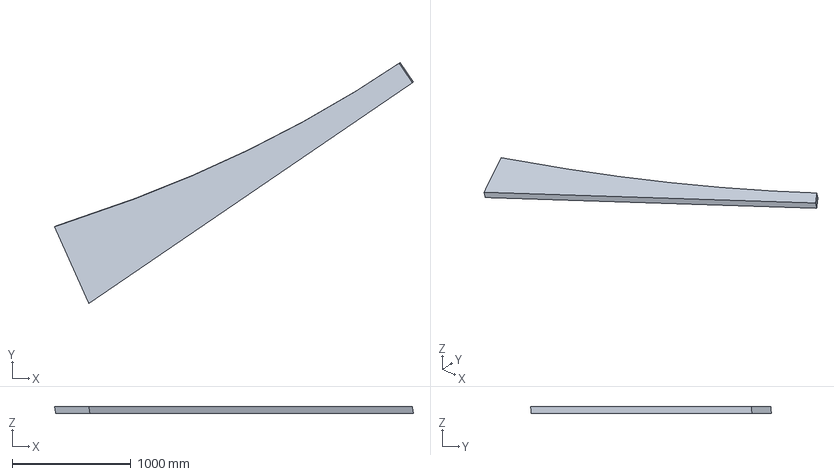
[picture p76: CAD file, 2026-08-25]
data/fabrication/inner_ribs_0_0_fab.stp
3017.9 x 2025.8 x 60.0 mm
inner_ribs_0_0_fab 1.1
inner_ribs_0_0_fab 1.2
