BRG-research/compas_tf/data/fabrication/inner_beams_1_0_fab.stp

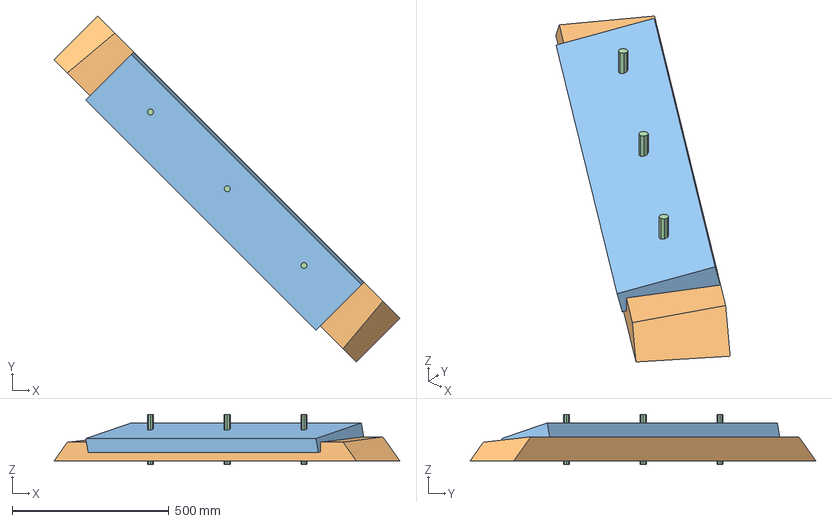
[picture p79: CAD file, 2026-08-25]
data/fabrication/inner_beams_1_0_fab.stp
1104.2 x 1104.2 x 160.0 mm
inner_beams_1_0_fab 1.1
inner_beams_1_0_fab 1.2
inner_beams_1_0_fab 1.3
inner_beams_1_0_fab 1.4
inner_beams_1_0_fab 1.5
inner_beams_1_0_fab 1.6
