BRG-research/compas_tf/data/fabrication/inner_beams_1_0_preview.obj

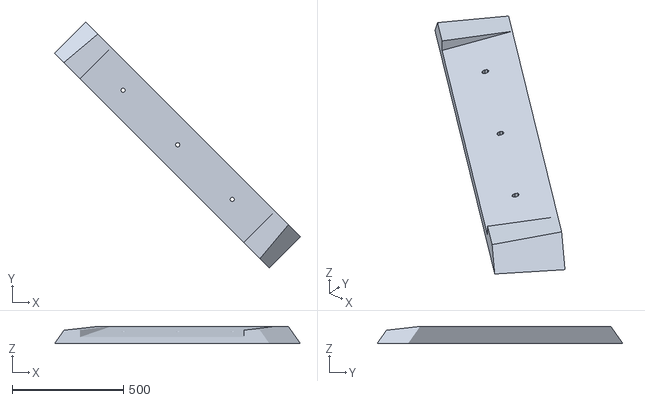
[picture p80: CAD file, 2026-08-25]
data/fabrication/inner_beams_1_0_preview.obj
1104.2 x 1104.2 x 77.2
