BRG-research/compas_tf/data/fabrication/column_0_fab.stp

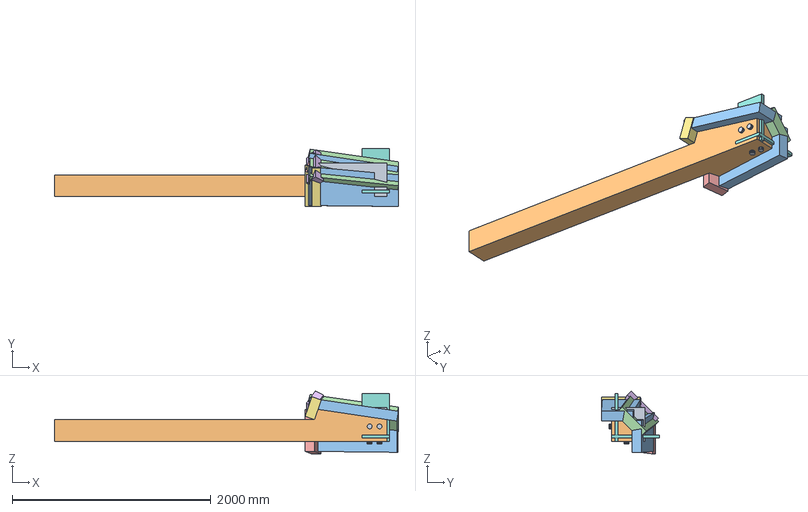
[picture p81: CAD file, 2026-08-25]
data/fabrication/column_0_fab.stp
3465.8 x 585.0 x 634.1 mm
column_0_fab 1.1
column_0_fab 1.2
column_0_fab 1.3
column_0_fab 1.4
column_0_fab 1.5
column_0_fab 1.6
column_0_fab 1.7
column_0_fab 1.8
column_0_fab 1.9
column_0_fab 1.10
column_0_fab 1.11
column_0_fab 1.12
column_0_fab 1.13
column_0_fab 1.14
