BRG-research/compas_tf/data/fabrication/connector_wedge_0_preview.obj

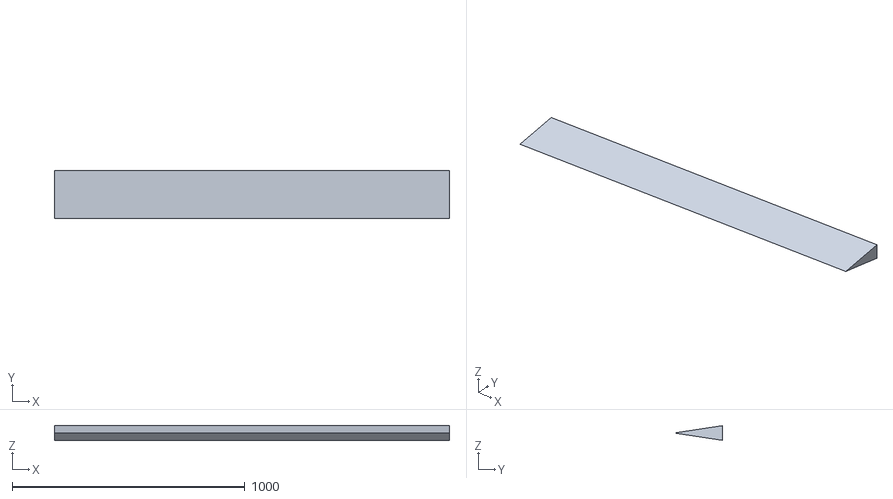
[picture p82: CAD file, 2026-08-25]
data/fabrication/connector_wedge_0_preview.obj
1698.8 x 208.5 x 63.5
