BRG-research/compas_tf/data/fabrication/beds_0_preview.obj

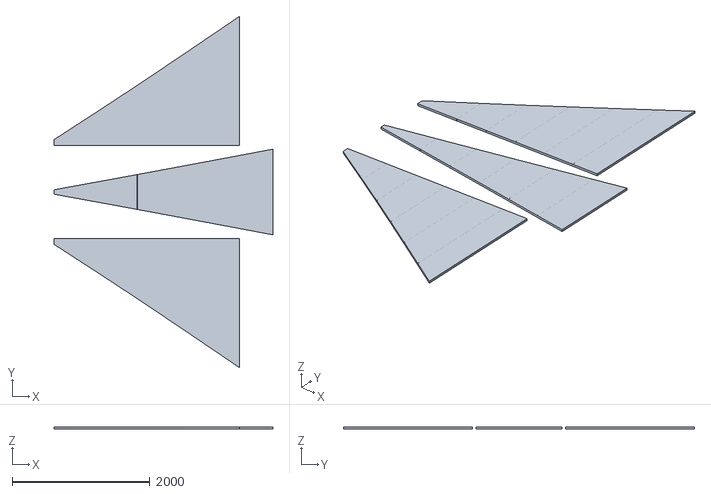
[picture p83: CAD file, 2026-08-25]
data/fabrication/beds_0_preview.obj
3175.0 x 5092.7 x 27.5
