BRG-research/compas_tf/data/fabrication/oculus_side_tsections_0_preview.obj

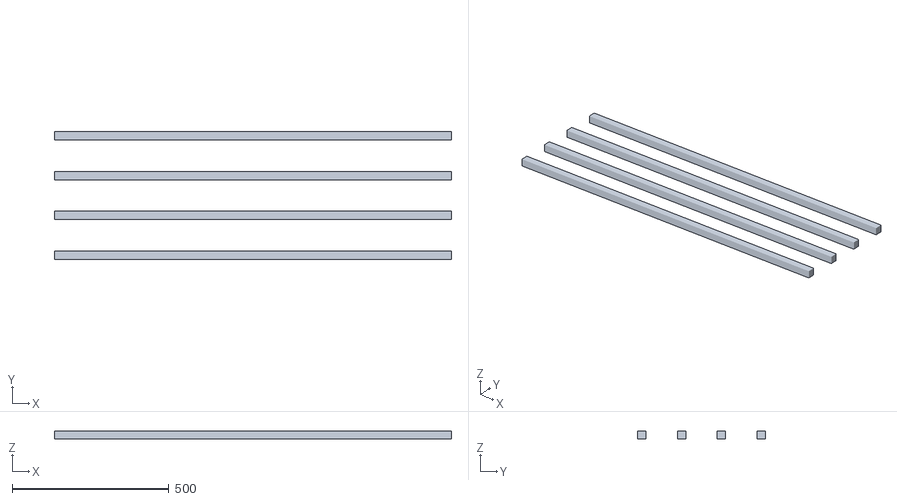
[picture p84: CAD file, 2026-08-20]
data/fabrication/oculus_side_tsections_0_preview.obj
1267.2 x 408.0 x 27.0
