BRG-research/compas_tf/data/fabrication/oculus_plate_0_fab.stp

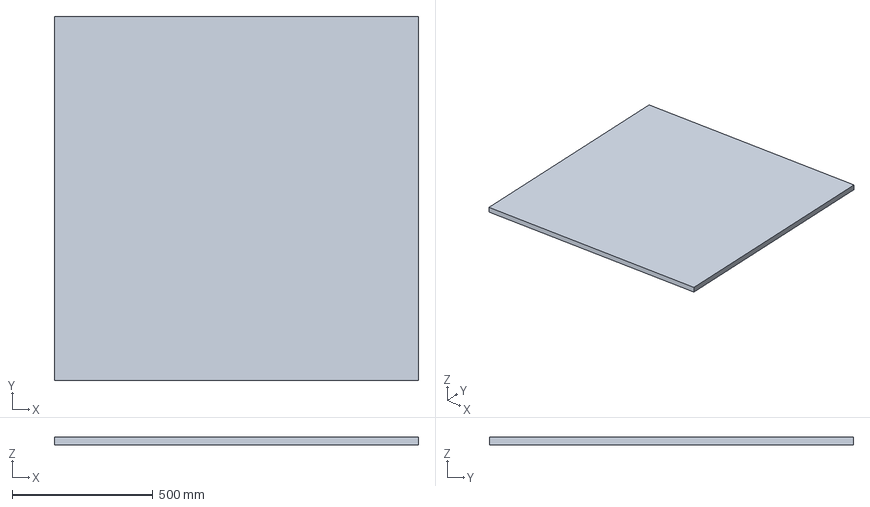
[picture p85: CAD file, 2026-08-20]
data/fabrication/oculus_plate_0_fab.stp
1294.2 x 1294.2 x 27.0 mm
oculus_plate_0_fab 3.1
oculus_plate_0_fab 3.2
