BRG-research/compas_tf/data/fabrication/oculus_plate_0_preview.obj

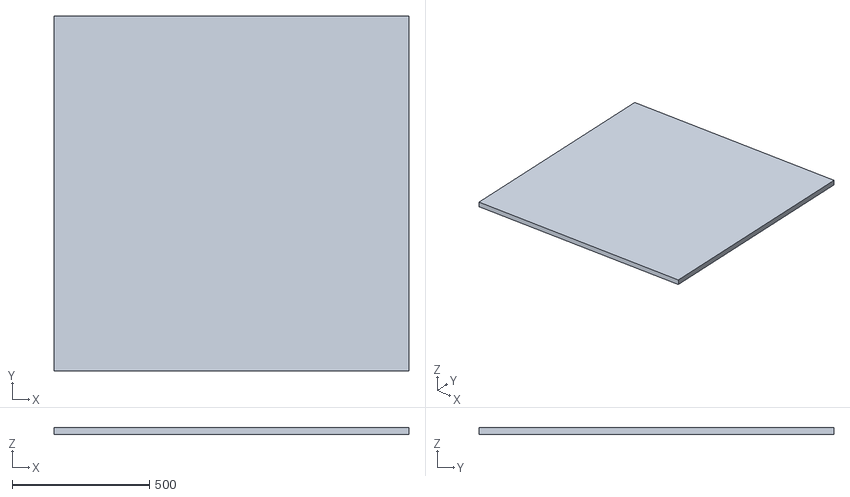
[picture p86: CAD file, 2026-08-20]
data/fabrication/oculus_plate_0_preview.obj
1294.2 x 1294.2 x 27.0
