BRG-research/compas_tf/data/fabrication/oculus_side_plates_0_preview.obj

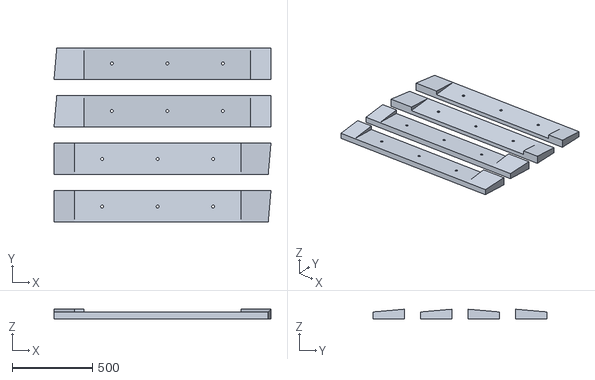
[picture p87: CAD file, 2026-08-20]
data/fabrication/oculus_side_plates_0_preview.obj
1354.2 x 1088.0 x 60.0
