BRG-research/compas_tf/data/fabrication/tsections_0_preview.obj

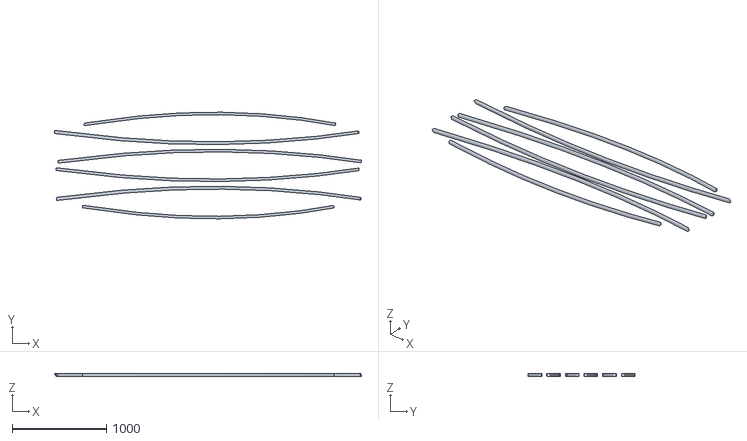
[picture p88: CAD file, 2026-08-20]
data/fabrication/tsections_0_preview.obj
3255.2 x 1130.6 x 27.0
