BRG-research/compas_tf/data/fabrication/outer_ribs_0_0_preview.obj

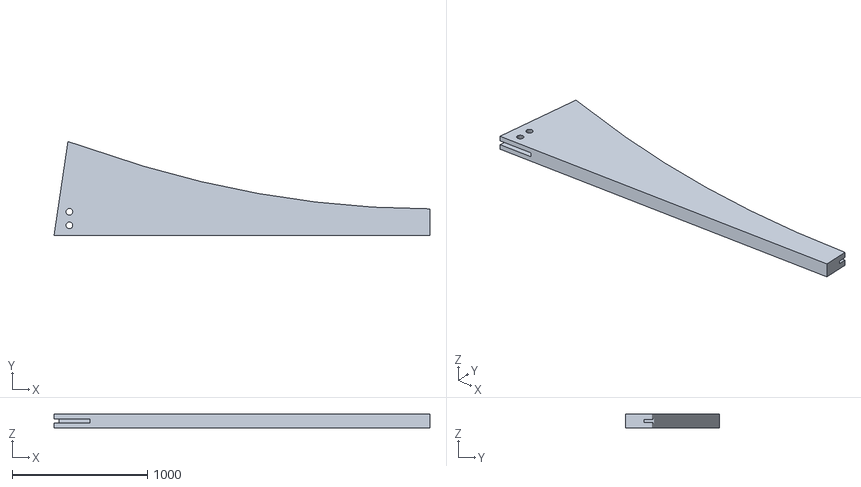
[picture p89: CAD file, 2026-08-20]
data/fabrication/outer_ribs_0_0_preview.obj
2780.0 x 694.8 x 100.0
