BRG-research/compas_tf/data/fabrication/oculus_side_tsections_0_fab.stp

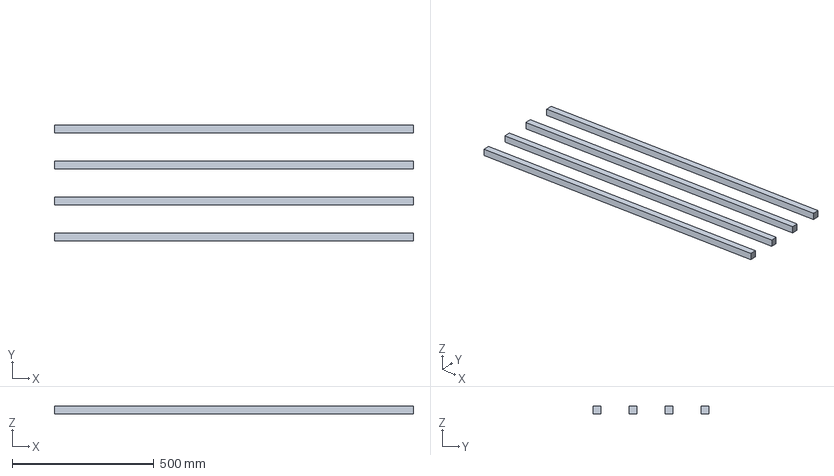
[picture p90: CAD file, 2026-08-20]
data/fabrication/oculus_side_tsections_0_fab.stp
1267.2 x 408.0 x 27.0 mm
oculus_side_tsections_0_fab 2.1
oculus_side_tsections_0_fab 2.2
oculus_side_tsections_0_fab 2.3
oculus_side_tsections_0_fab 2.4
oculus_side_tsections_0_fab 2.5
oculus_side_tsections_0_fab 2.6
oculus_side_tsections_0_fab 2.7
oculus_side_tsections_0_fab 2.8
