BRG-research/compas_tf/data/fabrication/wedges_inner_beams_0_preview.obj

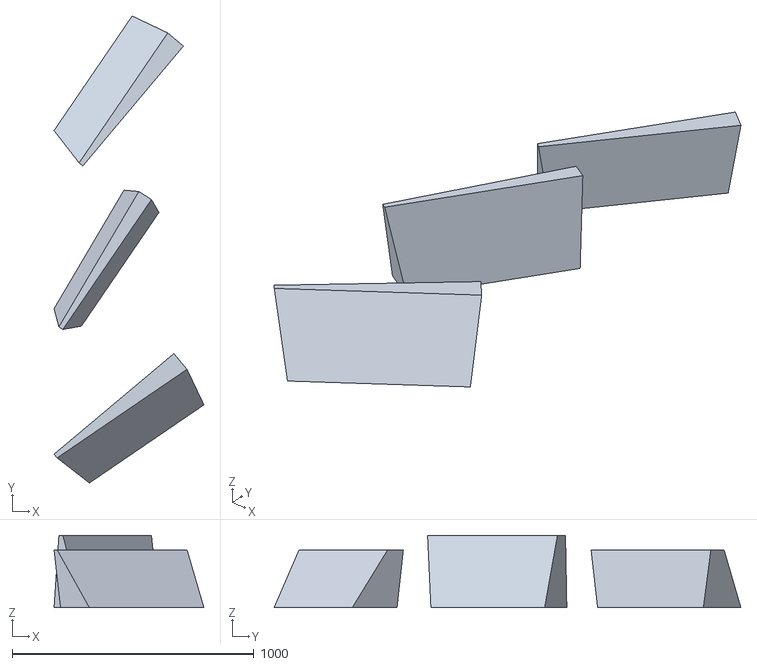
[picture p91: CAD file, 2026-08-20]
data/fabrication/wedges_inner_beams_0_preview.obj
620.7 x 1932.8 x 300.0
