BRG-research/compas_tf/data/fabrication/oculus_side_plates_0_fab.stp

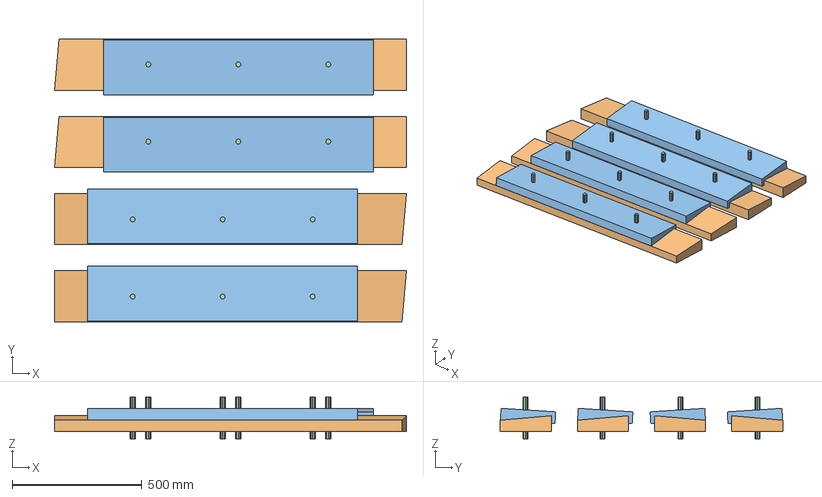
[picture p92: CAD file, 2026-08-20]
data/fabrication/oculus_side_plates_0_fab.stp
1354.2 x 1088.0 x 160.0 mm
oculus_side_plates_0_fab 1.1
oculus_side_plates_0_fab 1.2
oculus_side_plates_0_fab 1.3
oculus_side_plates_0_fab 1.4
oculus_side_plates_0_fab 1.5
oculus_side_plates_0_fab 1.6
oculus_side_plates_0_fab 1.7
oculus_side_plates_0_fab 1.8
oculus_side_plates_0_fab 1.9
oculus_side_plates_0_fab 1.10
oculus_side_plates_0_fab 1.11
oculus_side_plates_0_fab 1.12
oculus_side_plates_0_fab 1.13
oculus_side_plates_0_fab 1.14
oculus_side_plates_0_fab 1.15
oculus_side_plates_0_fab 1.16
oculus_side_plates_0_fab 1.17
oculus_side_plates_0_fab 1.18
oculus_side_plates_0_fab 1.19
oculus_side_plates_0_fab 1.20
oculus_side_plates_0_fab 1.21
oculus_side_plates_0_fab 1.22
oculus_side_plates_0_fab 1.23
oculus_side_plates_0_fab 1.24
