BRG-research/compas_tf/data/fabrication/inner_ribs_0_0_preview.obj

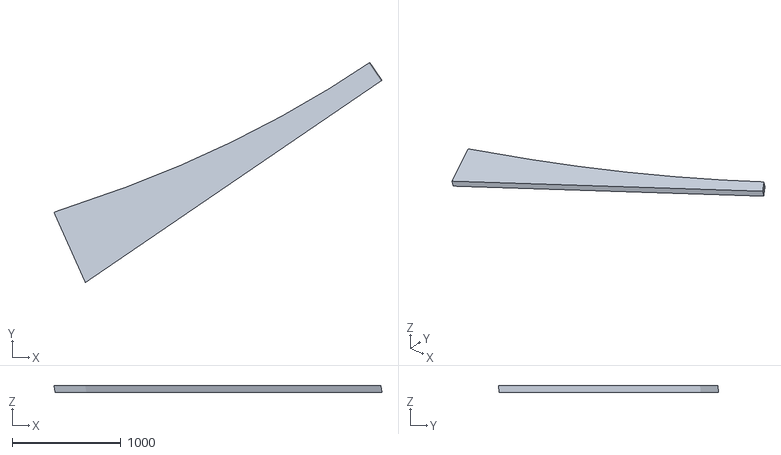
[picture p93: CAD file, 2026-08-20]
data/fabrication/inner_ribs_0_0_preview.obj
3017.9 x 2025.8 x 60.0
