BRG-research/compas_tf/docs/_images/step_0.png

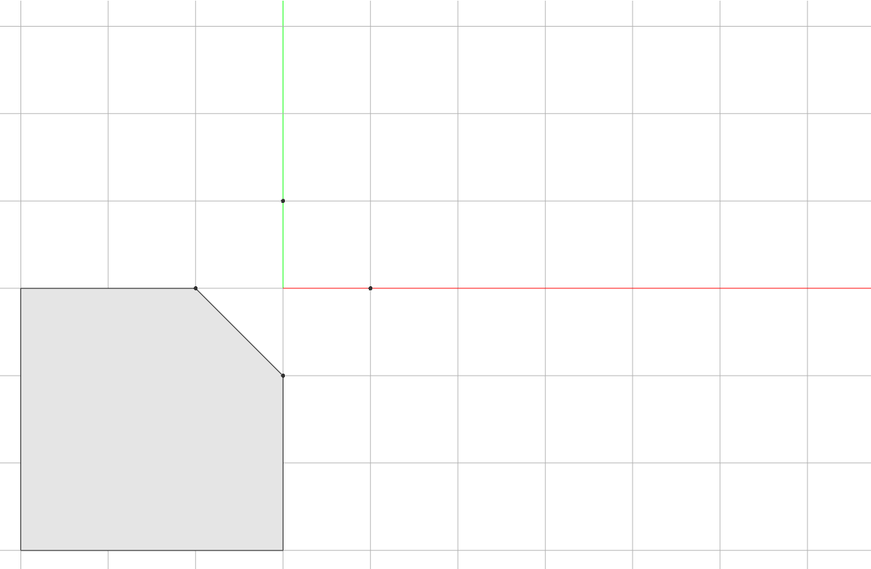
docs/_images/step_0.png
