BRG-research/compas_tf/docs/_images/step_1_a.png

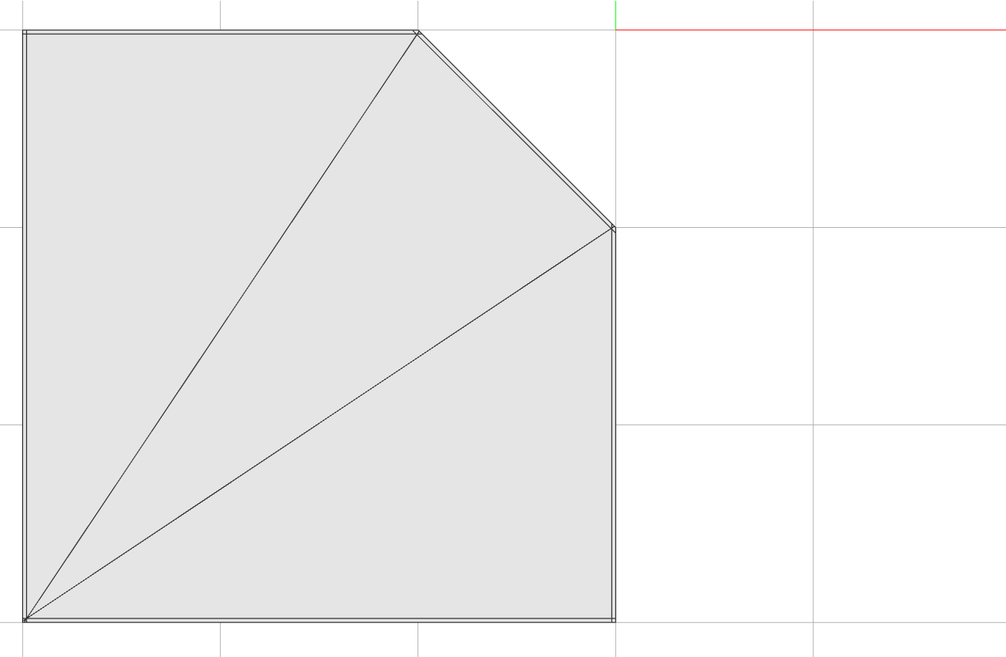
docs/_images/step_1_a.png
