BRG-research/compas_tf/docs/_images/step_1_b.png

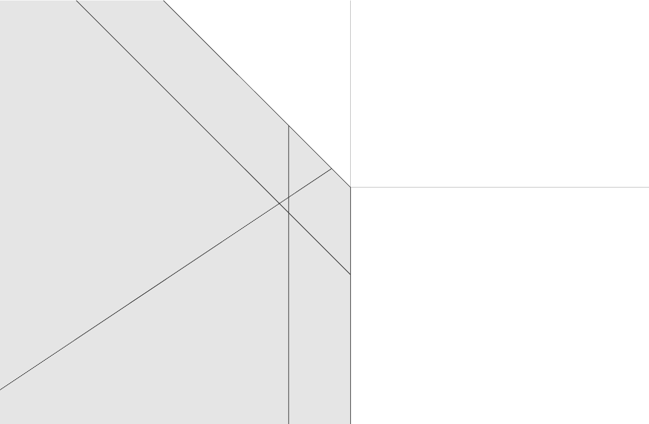
docs/_images/step_1_b.png
