BRG-research/compas_tf/docs/_images/step_2.png

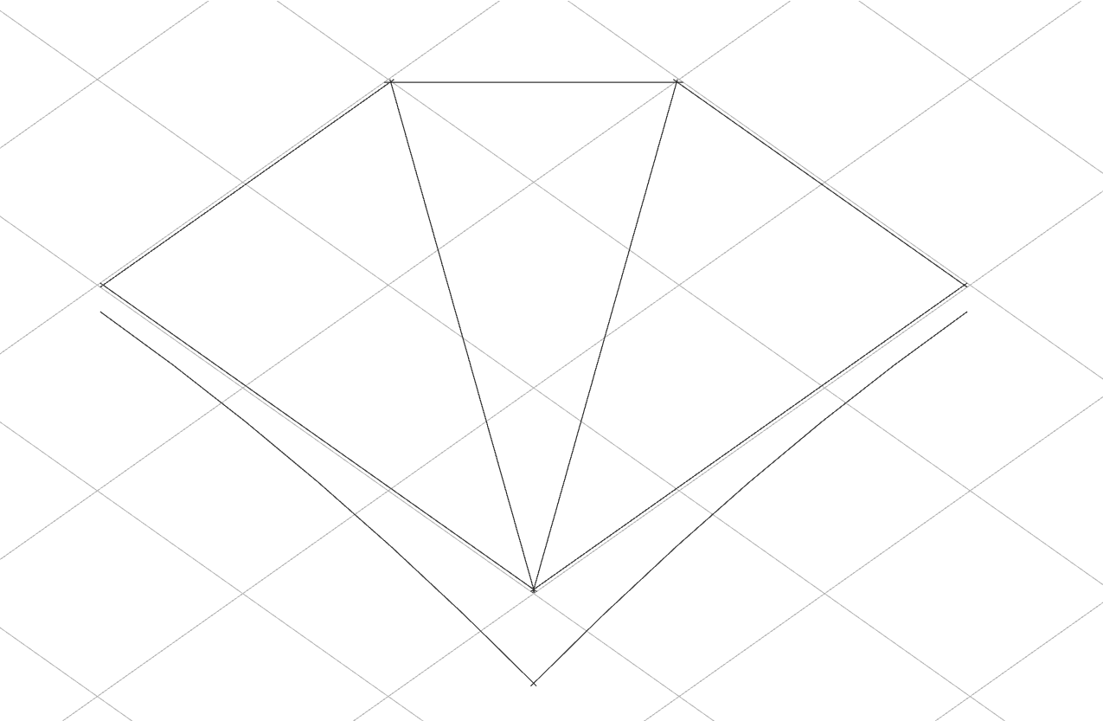
docs/_images/step_2.png
